COSMIIC-Inc/Implantables-PM-Hardware/Mechanical Design CAD Files/SolidWorks Native Files/NNP-DWG-115-005-000 SA, Battery.SLDASM

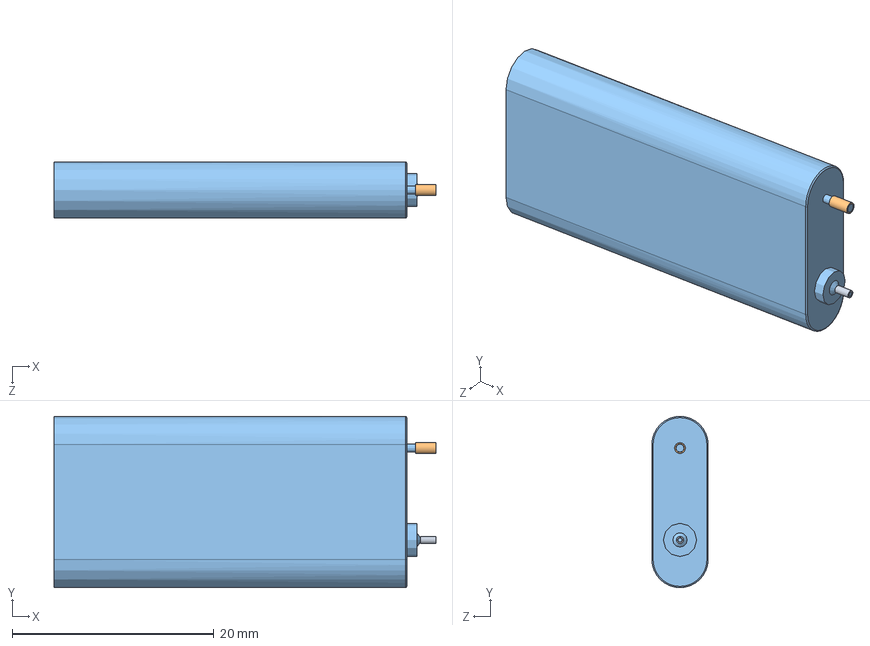
[picture p15: CAD file, 2024-08-27]
Mechanical Design CAD Files/SolidWorks Native Files/NNP-DWG-115-005-000 SA, Battery.SLDASM
37.9 x 17.0 x 5.59 mm
NNP-DWG-110-023-000 Battery, Quallion
NNP-DWG-110-024-001 Battery, Large Sleeve
NNP-DWG-110-024-002 Battery, Small Sleeve
