COSMIIC-Inc/Implantables-PM-Hardware/Mechanical Design CAD Files/SolidWorks Native Files/NNP-DWG-130-011-000 Balseal, Conductor.SLDPRT

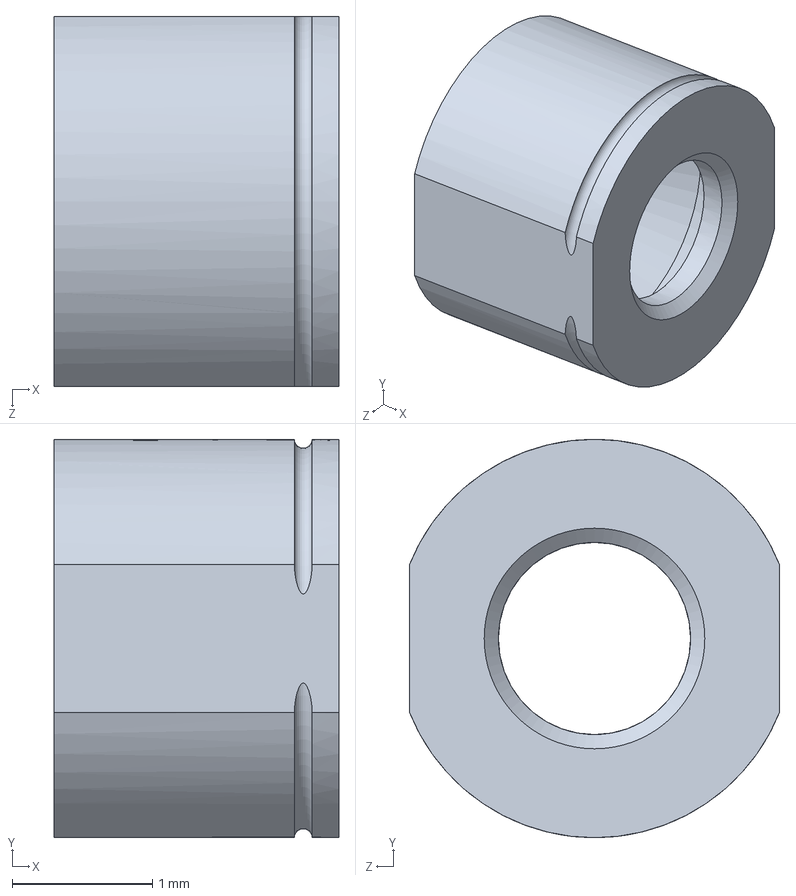
[picture p18: CAD file, 2024-08-27]
Mechanical Design CAD Files/SolidWorks Native Files/NNP-DWG-130-011-000 Balseal, Conductor.SLDPRT
2.03 x 2.84 x 2.64 mm
