COSMIIC-Inc/Implantables-PM-Hardware/Mechanical Design CAD Files/STEP Files/NNP-MAT-150-009-000 NuSil Med1-4213.STEP

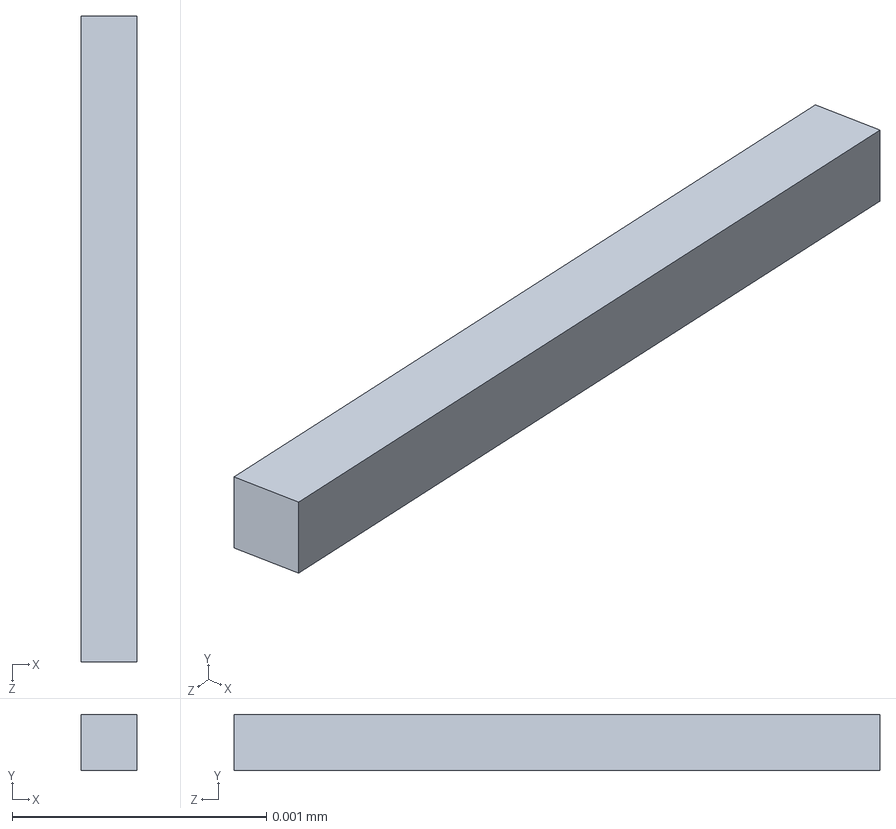
[picture p19: CAD file, 2024-08-27]
Mechanical Design CAD Files/STEP Files/NNP-MAT-150-009-000 NuSil Med1-4213.STEP
0.000221 x 0.000221 x 0.00254 mm
