COSMIIC-Inc/Implantables-PM-Hardware/Mechanical Design CAD Files/STEP Files/NNP-DWG-110-019-000 Capacitor, 0.47 uF.STEP

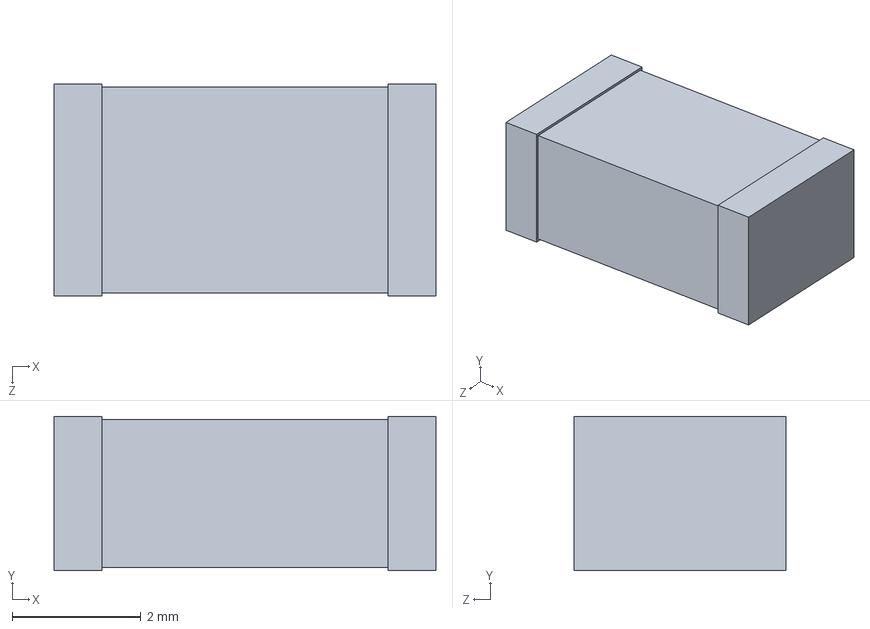
[picture p20: CAD file, 2024-08-27]
Mechanical Design CAD Files/STEP Files/NNP-DWG-110-019-000 Capacitor, 0.47 uF.STEP
5.94 x 2.40 x 3.30 mm
