COSMIIC-Inc/Implantables-PM-Hardware/Mechanical Design CAD Files/SolidWorks Native Files/NNP-DWG-110-024-001 Battery, Large Sleeve.SLDPRT

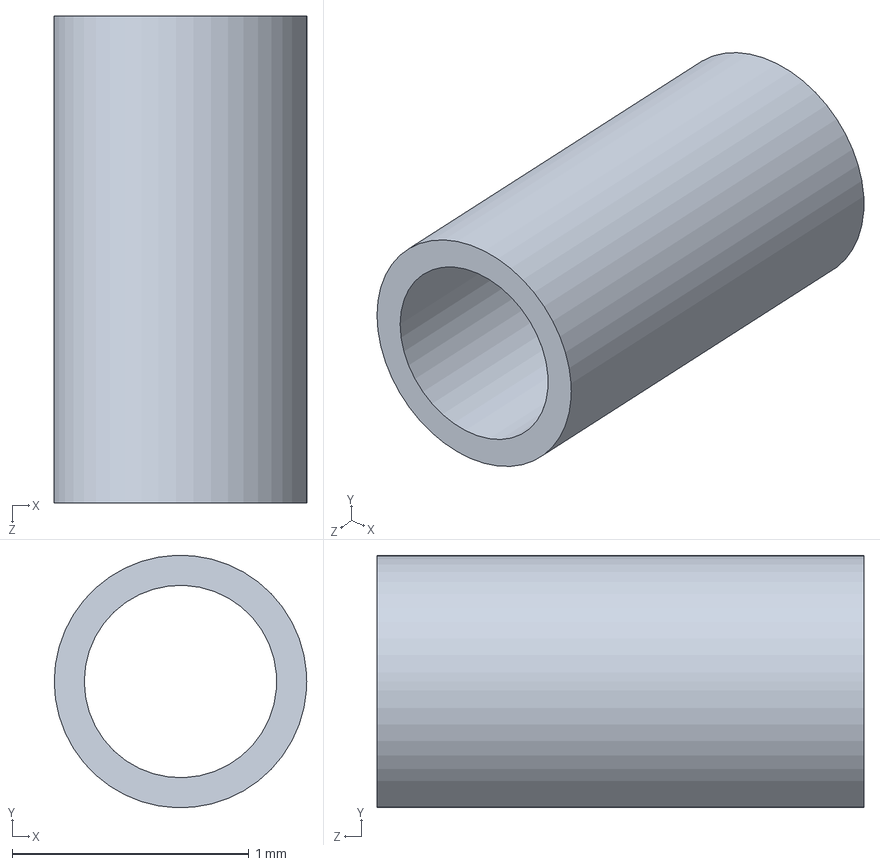
[picture p21: CAD file, 2024-08-27]
Mechanical Design CAD Files/SolidWorks Native Files/NNP-DWG-110-024-001 Battery, Large Sleeve.SLDPRT
1.07 x 1.07 x 2.06 mm
