COSMIIC-Inc/Implantables-PM-Hardware/Mechanical Design CAD Files/STEP Files/NNP-DWG-110-021-000 Insulator Nest, Top.STEP

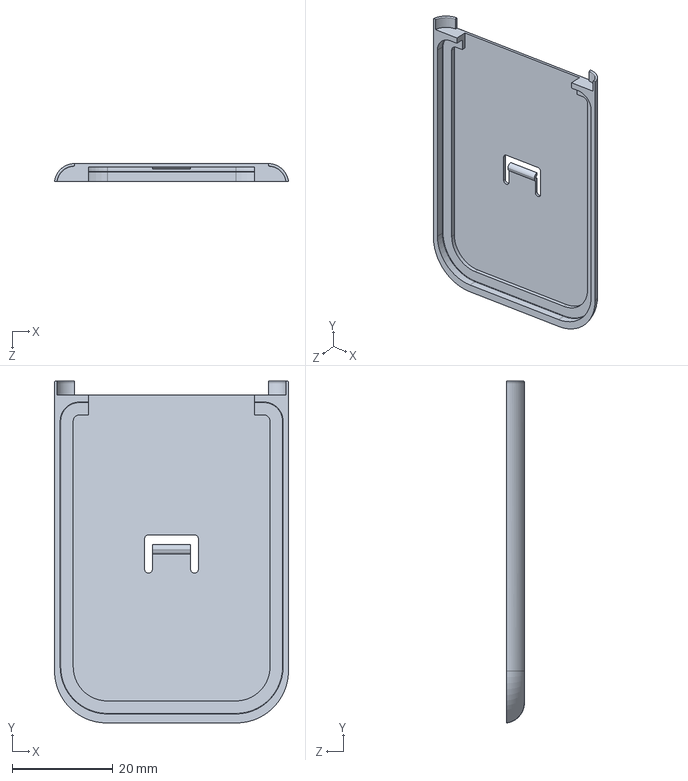
[picture p22: CAD file, 2024-08-27]
Mechanical Design CAD Files/STEP Files/NNP-DWG-110-021-000 Insulator Nest, Top.STEP
46.6 x 68.0 x 3.56 mm
