COSMIIC-Inc/Implantables-PM-Hardware/Mechanical Design CAD Files/SolidWorks Native Files/NNP-DWG-110-009-000 Case, Uncut Half.SLDPRT

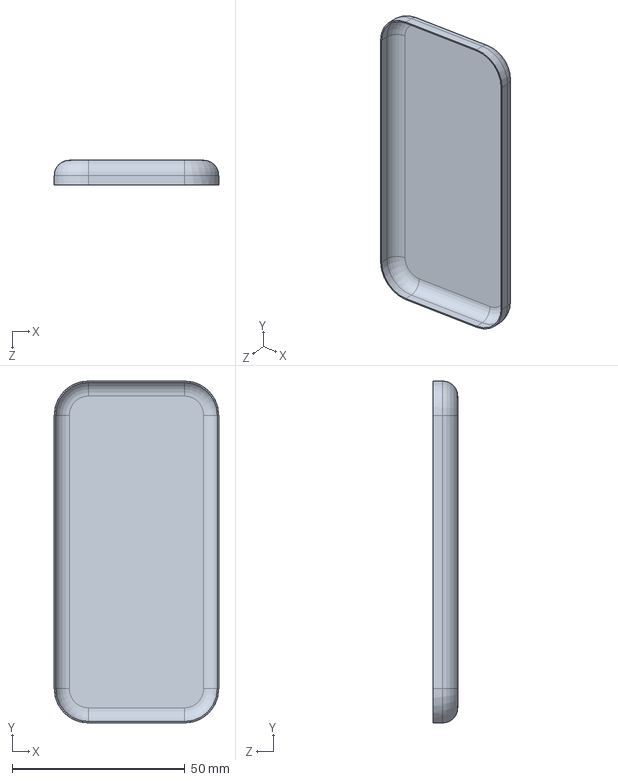
[picture p23: CAD file, 2024-08-27]
Mechanical Design CAD Files/SolidWorks Native Files/NNP-DWG-110-009-000 Case, Uncut Half.SLDPRT
47.7 x 99.1 x 7.11 mm
