COSMIIC-Inc/Implantables-PM-Hardware/Mechanical Design CAD Files/SolidWorks Native Files/NNP-DWG-110-013-000 Feedthrough Pin, Short.SLDPRT

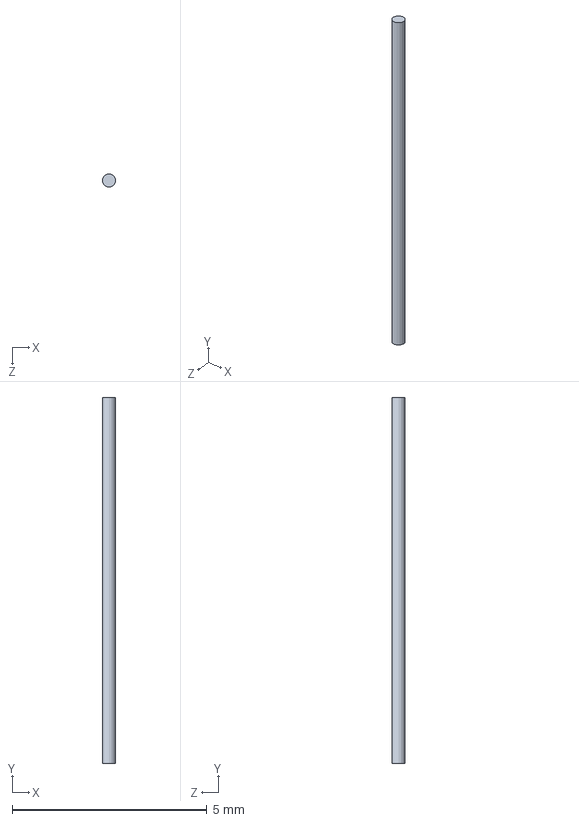
[picture p24: CAD file, 2024-08-27]
Mechanical Design CAD Files/SolidWorks Native Files/NNP-DWG-110-013-000 Feedthrough Pin, Short.SLDPRT
0.343 x 9.40 x 0.343 mm
