COSMIIC-Inc/Implantables-PM-Hardware/Mechanical Design CAD Files/STEP Files/NNP-DWG-110-008-000 BalSeal Block.STEP

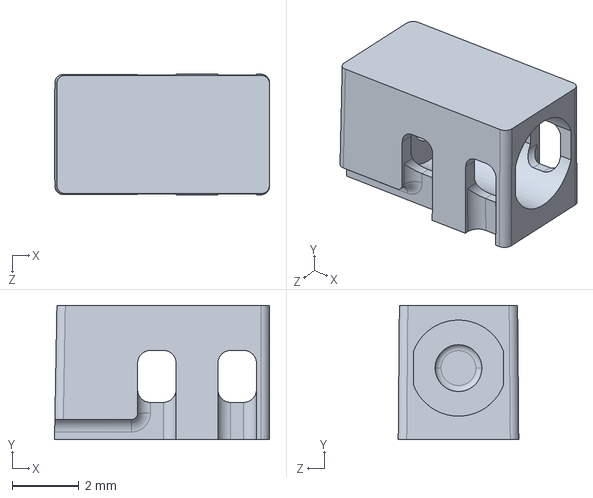
[picture p25: CAD file, 2024-08-27]
Mechanical Design CAD Files/STEP Files/NNP-DWG-110-008-000 BalSeal Block.STEP
6.42 x 4.01 x 3.60 mm
