COSMIIC-Inc/Implantables-PM-Hardware/Mechanical Design CAD Files/SolidWorks Native Files/NNP-DWG-110-003-000 Suture Skirt.SLDPRT

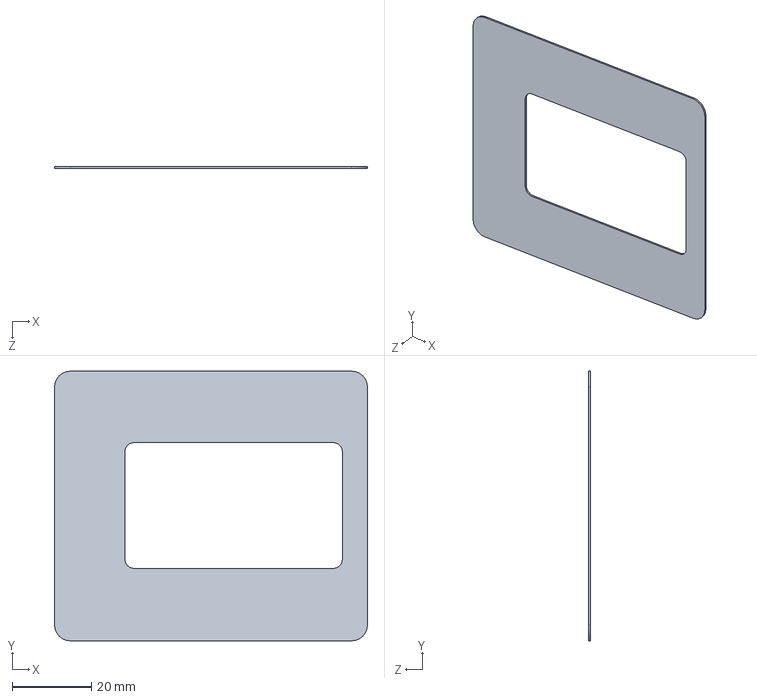
[picture p26: CAD file, 2024-08-27]
Mechanical Design CAD Files/SolidWorks Native Files/NNP-DWG-110-003-000 Suture Skirt.SLDPRT
79.0 x 68.1 x 0.5 mm
