COSMIIC-Inc/Implantables-PM-Hardware/Mechanical Design CAD Files/STEP Files/NNP-DWG-110-017-000 Power Module, Daughter Board.STEP

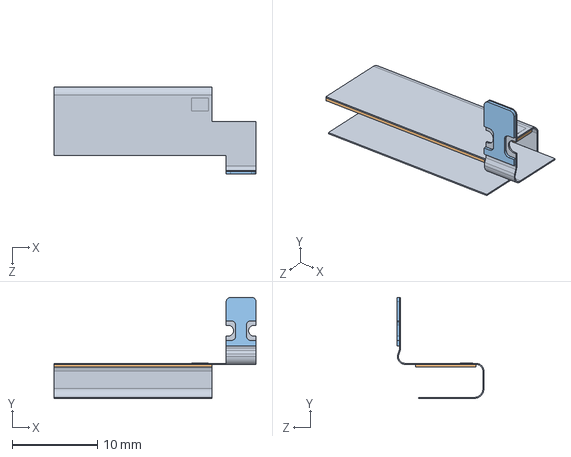
[picture p27: CAD file, 2024-08-27]
Mechanical Design CAD Files/STEP Files/NNP-DWG-110-017-000 Power Module, Daughter Board.STEP
23.7 x 11.9 x 10.2 mm
