COSMIIC-Inc/Implantables-PM-Hardware/Mechanical Design CAD Files/SolidWorks Native Files/NNP-DWG-110-020-000 Thermistor.SLDPRT

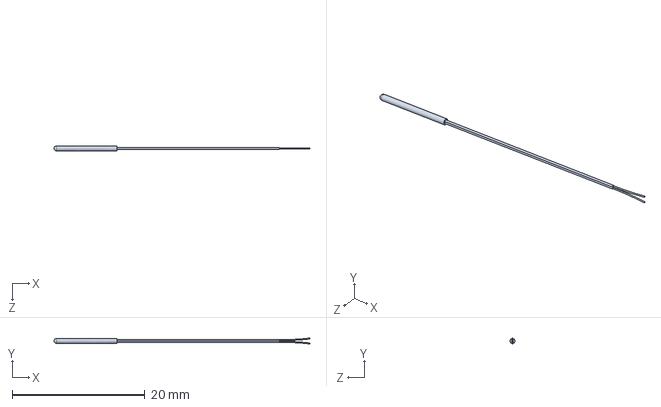
[picture p28: CAD file, 2024-08-27]
Mechanical Design CAD Files/SolidWorks Native Files/NNP-DWG-110-020-000 Thermistor.SLDPRT
38.6 x 0.891 x 0.761 mm
