COSMIIC-Inc/Implantables-PM-Hardware/Mechanical Design CAD Files/STEP Files/NNP-DWG-110-025-000 Recharge Coil.STEP

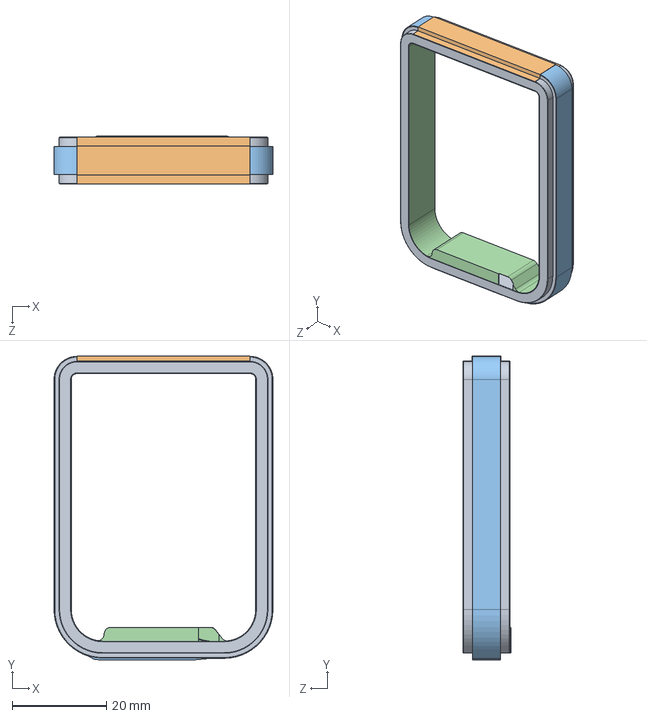
[picture p29: CAD file, 2024-08-27]
Mechanical Design CAD Files/STEP Files/NNP-DWG-110-025-000 Recharge Coil.STEP
46.5 x 64.5 x 10.2 mm
