COSMIIC-Inc/Implantables-PM-Hardware/Mechanical Design CAD Files/SolidWorks Native Files/NNP-DWG-110-015-000 Insulator, PM Feedthrough.SLDPRT

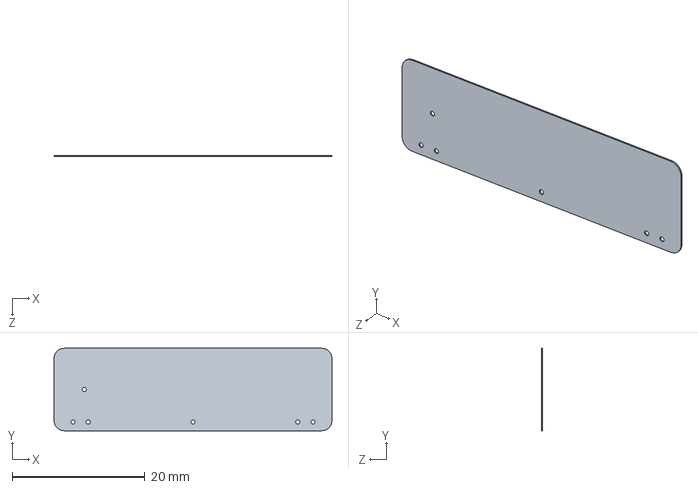
[picture p30: CAD file, 2024-08-27]
Mechanical Design CAD Files/SolidWorks Native Files/NNP-DWG-110-015-000 Insulator, PM Feedthrough.SLDPRT
41.9 x 12.4 x 0.19 mm
