COSMIIC-Inc/Implantables-PM-Hardware/Mechanical Design CAD Files/STEP Files/NNP-DWG-130-012-002 Balseal, Spring, CCW.STEP

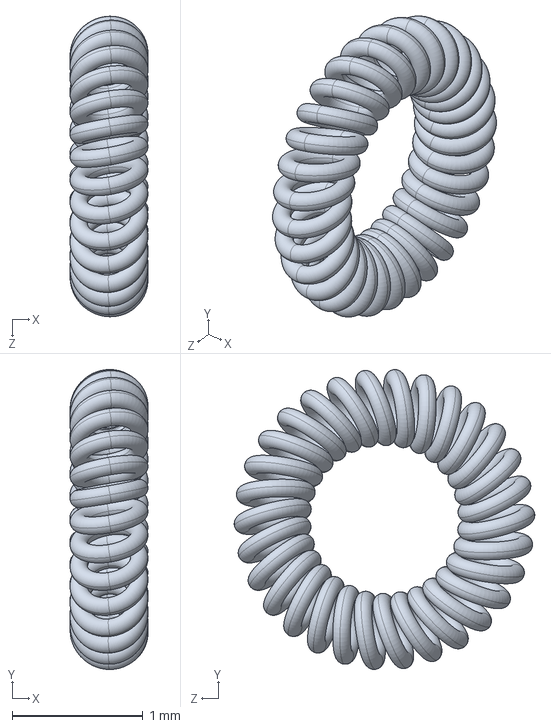
[picture p31: CAD file, 2024-08-27]
Mechanical Design CAD Files/STEP Files/NNP-DWG-130-012-002 Balseal, Spring, CCW.STEP
0.597 x 2.30 x 2.30 mm
