COSMIIC-Inc/Implantables-PM-Hardware/Mechanical Design CAD Files/SolidWorks Native Files/NNP-DWG-110-002-000 Port Plug, Body.SLDPRT

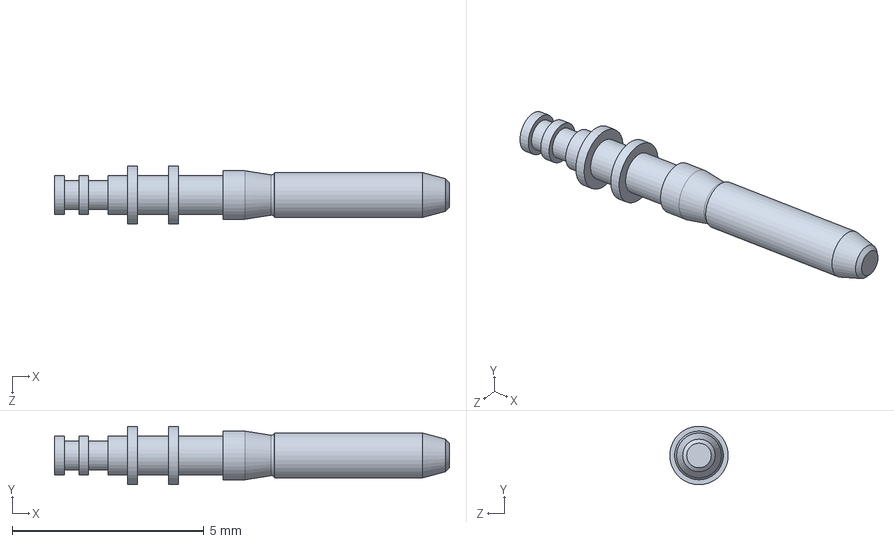
[picture p32: CAD file, 2024-08-27]
Mechanical Design CAD Files/SolidWorks Native Files/NNP-DWG-110-002-000 Port Plug, Body.SLDPRT
10.3 x 1.52 x 1.52 mm
