COSMIIC-Inc/Implantables-PM-Hardware/Mechanical Design CAD Files/SolidWorks Native Files/NNP-DWG-110-012-000 Lidthrough, Anchor Pin.SLDPRT

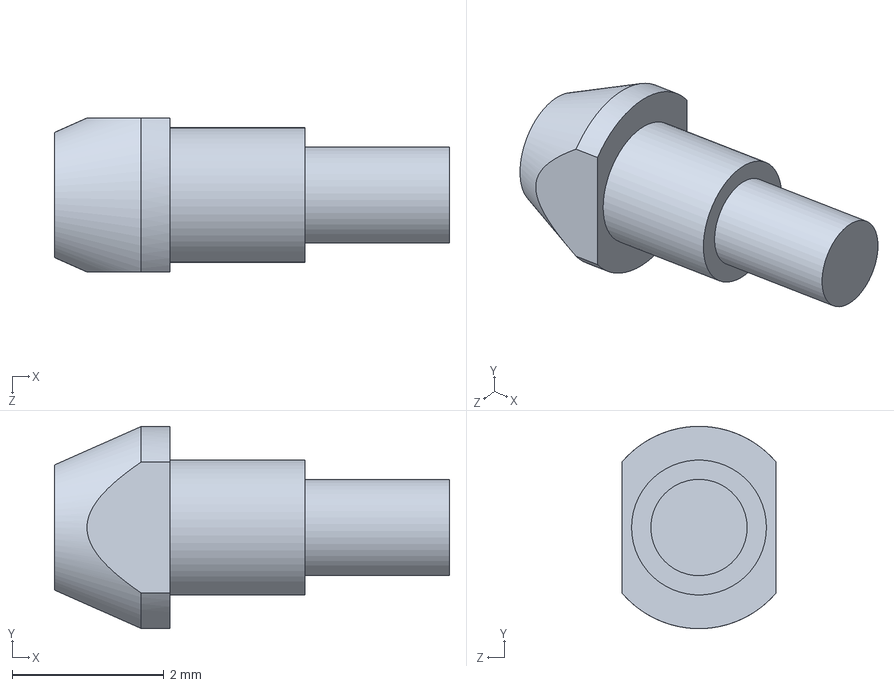
[picture p33: CAD file, 2024-08-27]
Mechanical Design CAD Files/SolidWorks Native Files/NNP-DWG-110-012-000 Lidthrough, Anchor Pin.SLDPRT
5.21 x 2.67 x 2.03 mm
