COSMIIC-Inc/Implantables-PM-Hardware/Mechanical Design CAD Files/STEP Files/NNP-DWG-110-022-000 Insulator Nest, Bottom.STEP

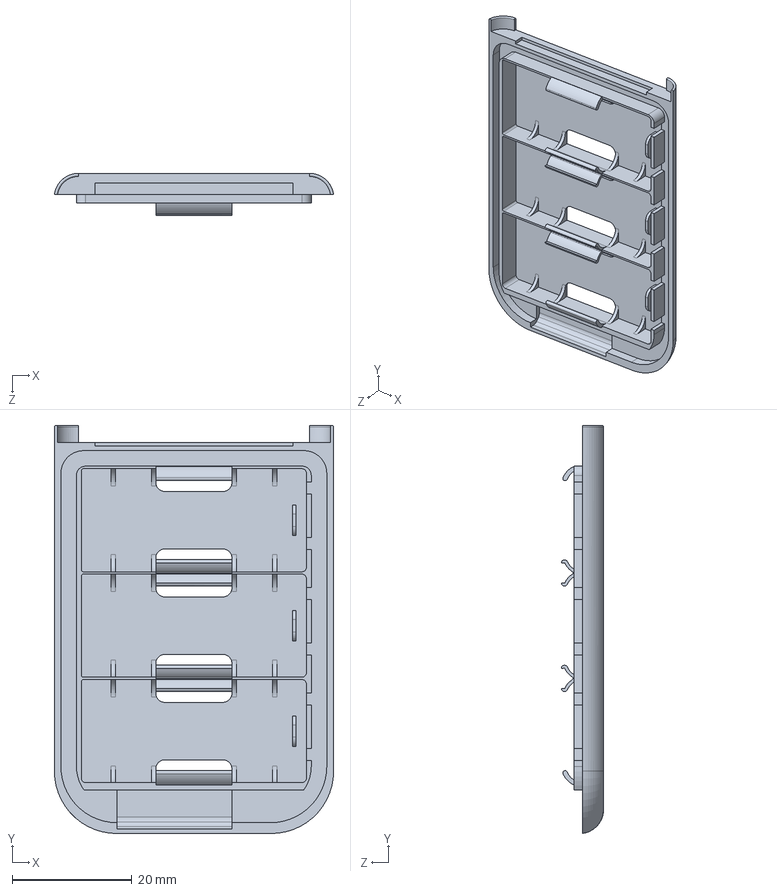
[picture p34: CAD file, 2024-08-27]
Mechanical Design CAD Files/STEP Files/NNP-DWG-110-022-000 Insulator Nest, Bottom.STEP
46.6 x 68.0 x 7.07 mm
