COSMIIC-Inc/Implantables-PM-Hardware/Mechanical Design CAD Files/SolidWorks Native Files/NNP-MAT-150-015-000 Kapton Tape.SLDPRT

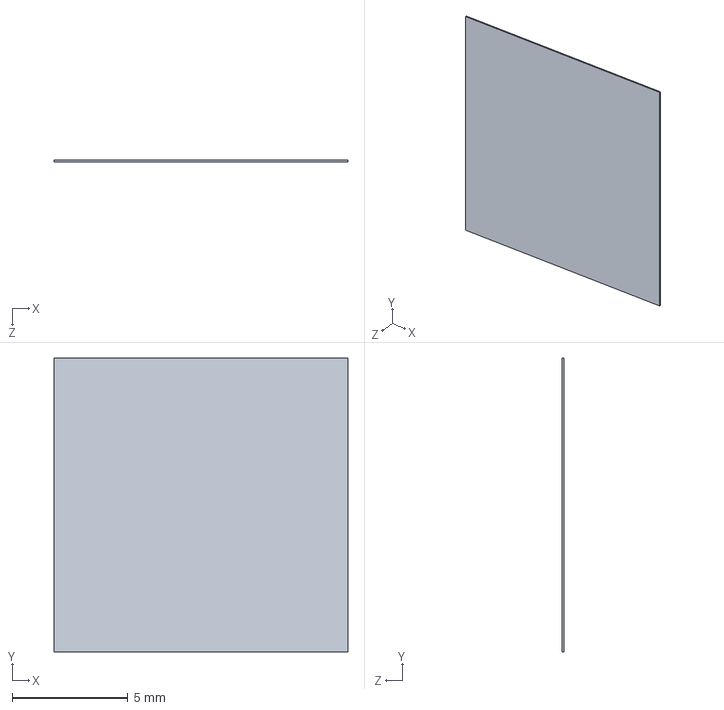
[picture p35: CAD file, 2024-08-27]
Mechanical Design CAD Files/SolidWorks Native Files/NNP-MAT-150-015-000 Kapton Tape.SLDPRT
12.7 x 12.7 x 0.07 mm
