COSMIIC-Inc/Implantables-PM-Hardware/Mechanical Design CAD Files/STEP Files/NNP-DWG-110-014-000 Lidthrough, Flange, 2 Port, Kryoflex.STEP

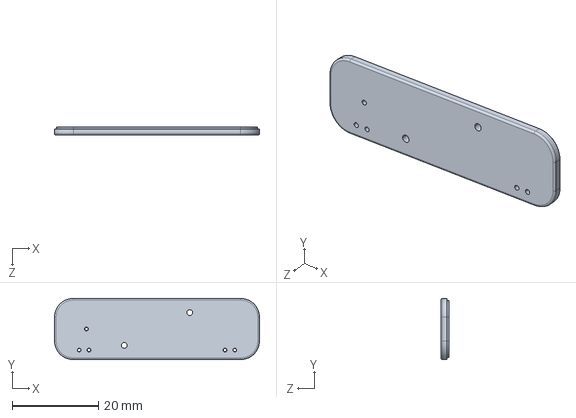
[picture p36: CAD file, 2024-08-27]
Mechanical Design CAD Files/STEP Files/NNP-DWG-110-014-000 Lidthrough, Flange, 2 Port, Kryoflex.STEP
47.7 x 14.2 x 1.91 mm
