COSMIIC-Inc/Implantables-PM-Hardware/Mechanical Design CAD Files/STEP Files/NNP-DWG-110-010-000 Case, Trimmed.STEP

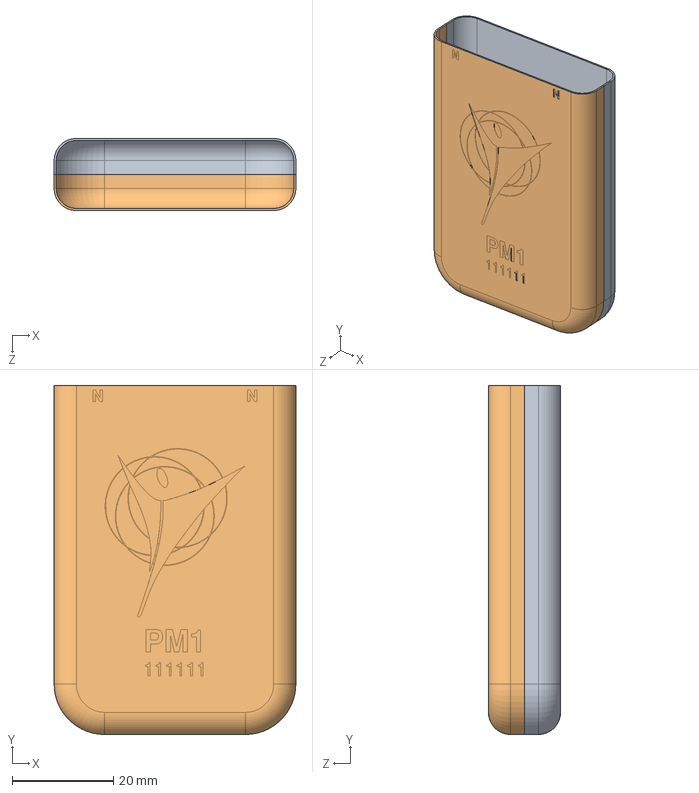
[picture p37: CAD file, 2024-08-27]
Mechanical Design CAD Files/STEP Files/NNP-DWG-110-010-000 Case, Trimmed.STEP
47.7 x 68.8 x 14.2 mm
NNP-DWG-110-009-000 Case, Uncut Half
NNP-DWG-110-009-000 Case, Uncut Half_Front Artwork
