COSMIIC-Inc/Implantables-PM-Hardware/Mechanical Design CAD Files/SolidWorks Native Files/NNP-DWG-110-005-000 Antenna Wire.SLDPRT

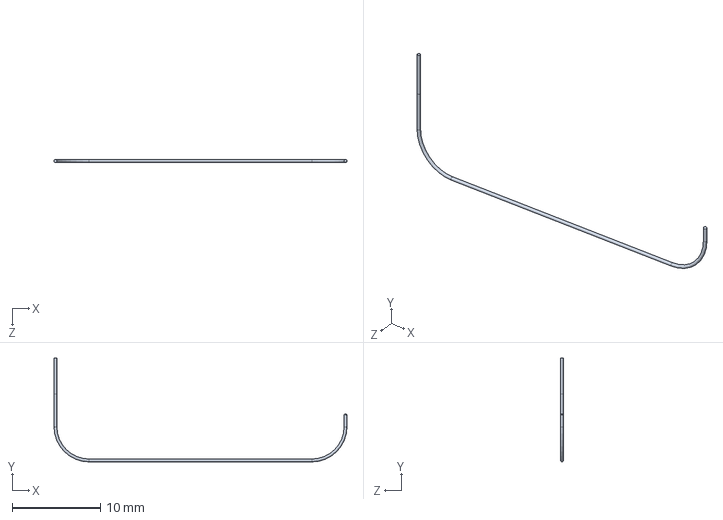
[picture p38: CAD file, 2024-08-27]
Mechanical Design CAD Files/SolidWorks Native Files/NNP-DWG-110-005-000 Antenna Wire.SLDPRT
33.2 x 11.8 x 0.33 mm
