COSMIIC-Inc/Implantables-PM-Hardware/Mechanical Design CAD Files/SolidWorks Native Files/NNP-DWG-110-016-000 Pre-Molded Header, 2-Port.SLDPRT

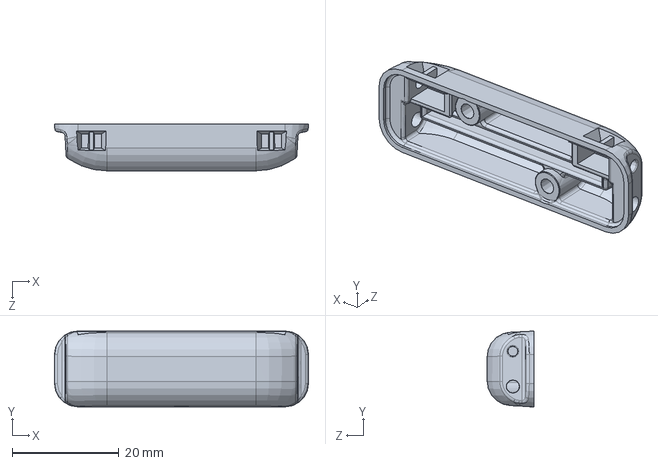
[picture p39: CAD file, 2024-08-27]
Mechanical Design CAD Files/SolidWorks Native Files/NNP-DWG-110-016-000 Pre-Molded Header, 2-Port.SLDPRT
47.7 x 14.2 x 8.76 mm
