COSMIIC-Inc/Implantables-PM-Hardware/Mechanical Design CAD Files/STEP Files/NNP-DWG-110-018-000 Capacitor, 0.22 uF.STEP

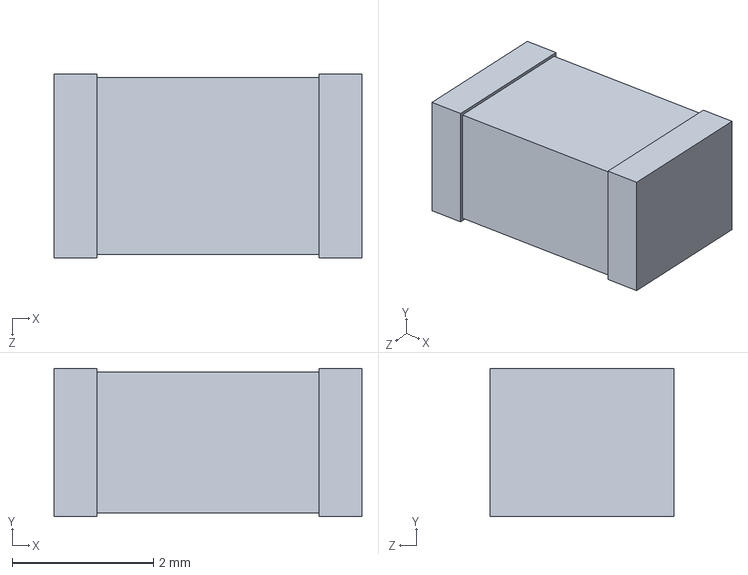
[picture p40: CAD file, 2024-08-27]
Mechanical Design CAD Files/STEP Files/NNP-DWG-110-018-000 Capacitor, 0.22 uF.STEP
4.36 x 2.10 x 2.60 mm
