COSMIIC-Inc/Implantables-PM-Hardware/Mechanical Design CAD Files/SolidWorks Native Files/NNP-DWG-110-004-000 Antenna Support.SLDPRT

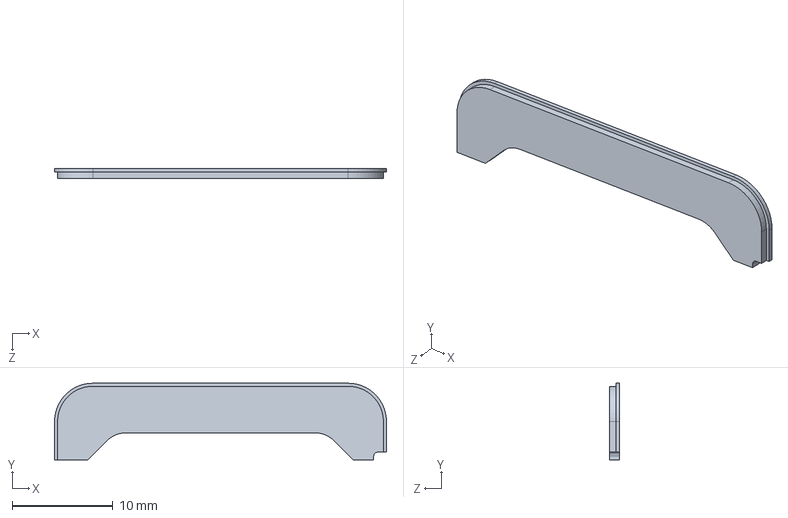
[picture p41: CAD file, 2024-08-27]
Mechanical Design CAD Files/SolidWorks Native Files/NNP-DWG-110-004-000 Antenna Support.SLDPRT
33.0 x 7.62 x 1.02 mm
