COSMIIC-Inc/Implantables-PM-Hardware/Mechanical Design CAD Files/SolidWorks Native Files/NNP-DWG-110-006-000 Case, Connection Wire.SLDPRT

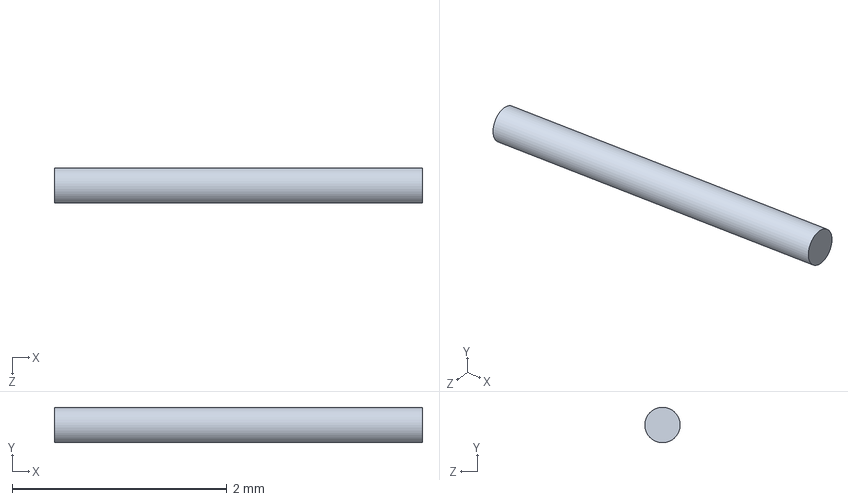
[picture p42: CAD file, 2024-08-27]
Mechanical Design CAD Files/SolidWorks Native Files/NNP-DWG-110-006-000 Case, Connection Wire.SLDPRT
3.43 x 0.33 x 0.33 mm
