COSMIIC-Inc/Implantables-PM-Hardware/Mechanical Design CAD Files/STEP Files/NNP-DWG-135-002-000 SA, Balseal, CW.STEP

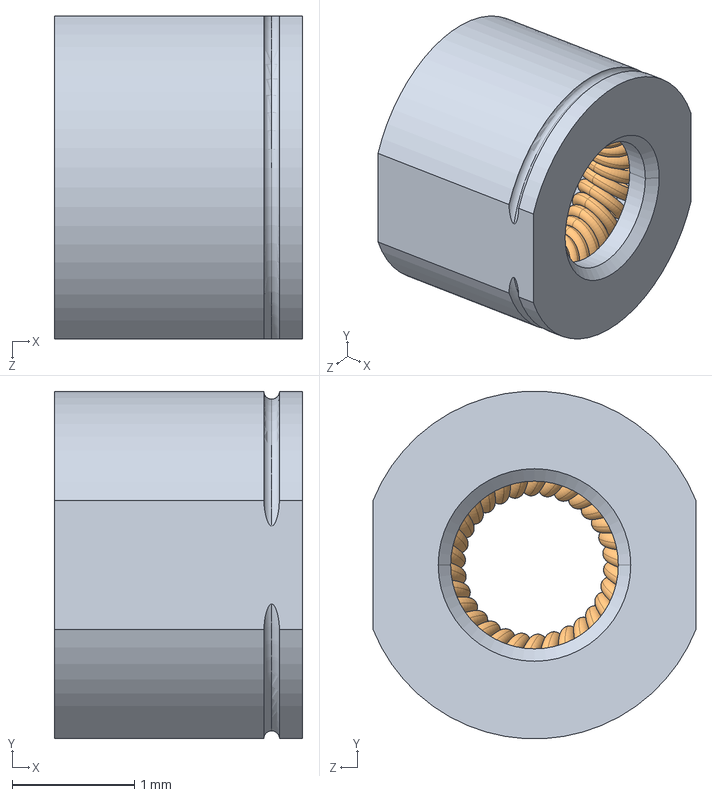
[picture p43: CAD file, 2024-08-27]
Mechanical Design CAD Files/STEP Files/NNP-DWG-135-002-000 SA, Balseal, CW.STEP
2.03 x 2.84 x 2.64 mm
NNP-DWG-130-011-000 Balseal, Conductor
NNP-DWG-130-012-001 Balseal, Spring, CW
NNP-DWG-130-013-001 Balseal, Washer, CW
