COSMIIC-Inc/Implantables-PM-Hardware/Mechanical Design CAD Files/STEP Files/NNP-DWG-110-007-000 Silicone Tube.STEP

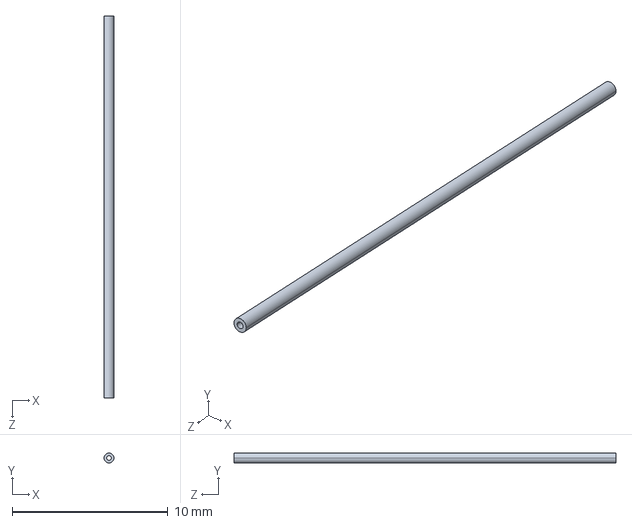
[picture p44: CAD file, 2024-08-27]
Mechanical Design CAD Files/STEP Files/NNP-DWG-110-007-000 Silicone Tube.STEP
0.635 x 0.635 x 24.5 mm
