COSMIIC-Inc/Implantables-PM-Hardware/Mechanical Design CAD Files/STEP Files/NNP-DWG-110-024-002 Battery, Small Sleeve.STEP

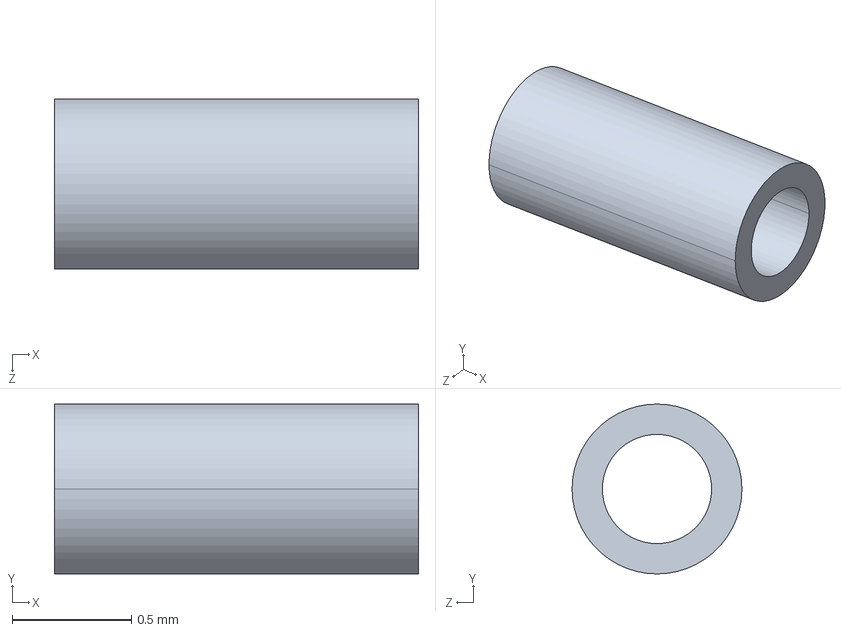
[picture p45: CAD file, 2024-08-27]
Mechanical Design CAD Files/STEP Files/NNP-DWG-110-024-002 Battery, Small Sleeve.STEP
1.52 x 0.711 x 0.711 mm
