COSMIIC-Inc/Implantables-PM-Hardware/Mechanical Design CAD Files/SolidWorks Native Files/NNP-DWG-110-007-000 Silicone Tube.SLDPRT

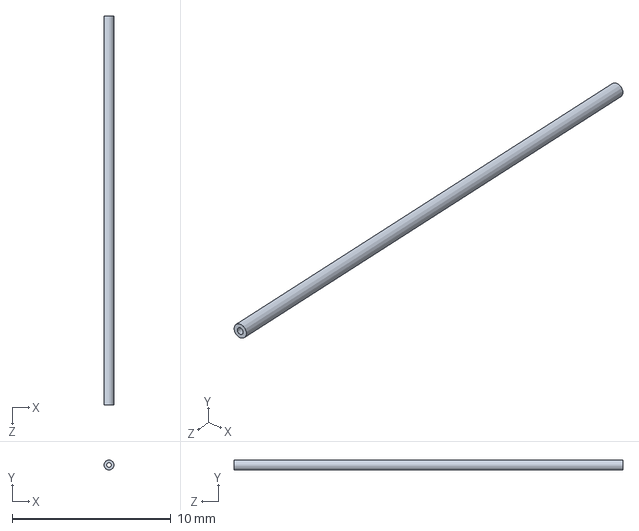
[picture p46: CAD file, 2024-08-27]
Mechanical Design CAD Files/SolidWorks Native Files/NNP-DWG-110-007-000 Silicone Tube.SLDPRT
0.635 x 0.632 x 24.5 mm
