COSMIIC-Inc/Implantables-PM-Hardware/Mechanical Design CAD Files/SolidWorks Native Files/NNP-DWG-110-021-000 Insulator Nest, Top.SLDPRT

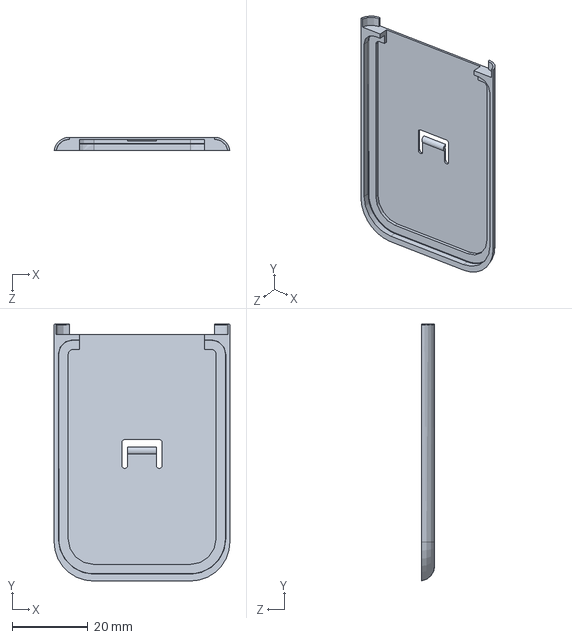
[picture p47: CAD file, 2024-08-27]
Mechanical Design CAD Files/SolidWorks Native Files/NNP-DWG-110-021-000 Insulator Nest, Top.SLDPRT
46.6 x 68.0 x 3.56 mm
