COSMIIC-Inc/Implantables-PM-Hardware/Mechanical Design CAD Files/SolidWorks Native Files/NNP-DWG-110-024-002 Battery, Small Sleeve.SLDPRT

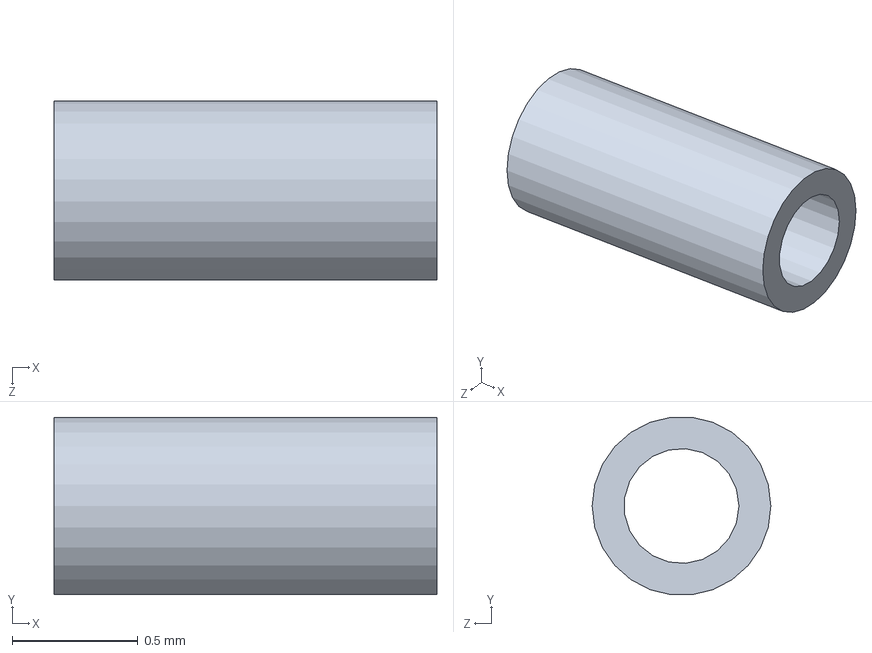
[picture p48: CAD file, 2024-08-27]
Mechanical Design CAD Files/SolidWorks Native Files/NNP-DWG-110-024-002 Battery, Small Sleeve.SLDPRT
1.52 x 0.706 x 0.711 mm
