COSMIIC-Inc/Implantables-PM-Hardware/Mechanical Design CAD Files/SolidWorks Native Files/NNP-DWG-135-002-000 SA, Balseal, CW.SLDASM

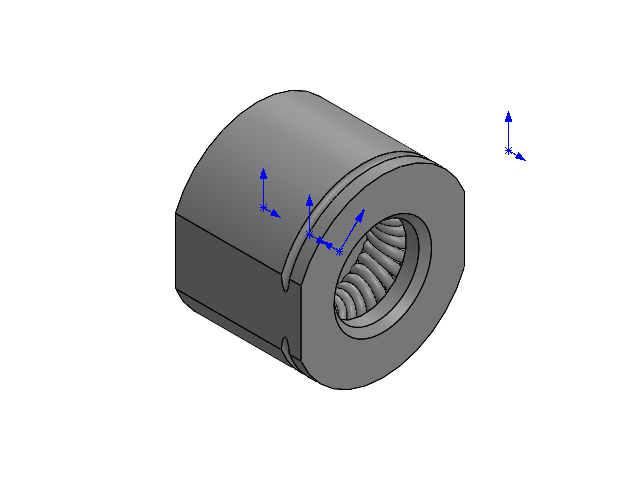
[picture p50: CAD file, 2024-08-27]
Mechanical Design CAD Files/SolidWorks Native Files/NNP-DWG-135-002-000 SA, Balseal, CW.SLDASM
NNP-DWG-130-011-000 Balseal, Conductor
NNP-DWG-130-012-001 Balseal, Spring, CW
NNP-DWG-130-013-001 Balseal, Washer, CW
