COSMIIC-Inc/Implantables-PM-Hardware/NNP-DWG-115-004-000 PCB Files/NNP-DWG-115-004-000 PM2 Schematics/51-2001-01-2_04 Power Module Schematic.pdf

ECN | DESCRIPTION | REV | DATE | REV. SHT. DWG. NO.

# ANALOG SIGNALS

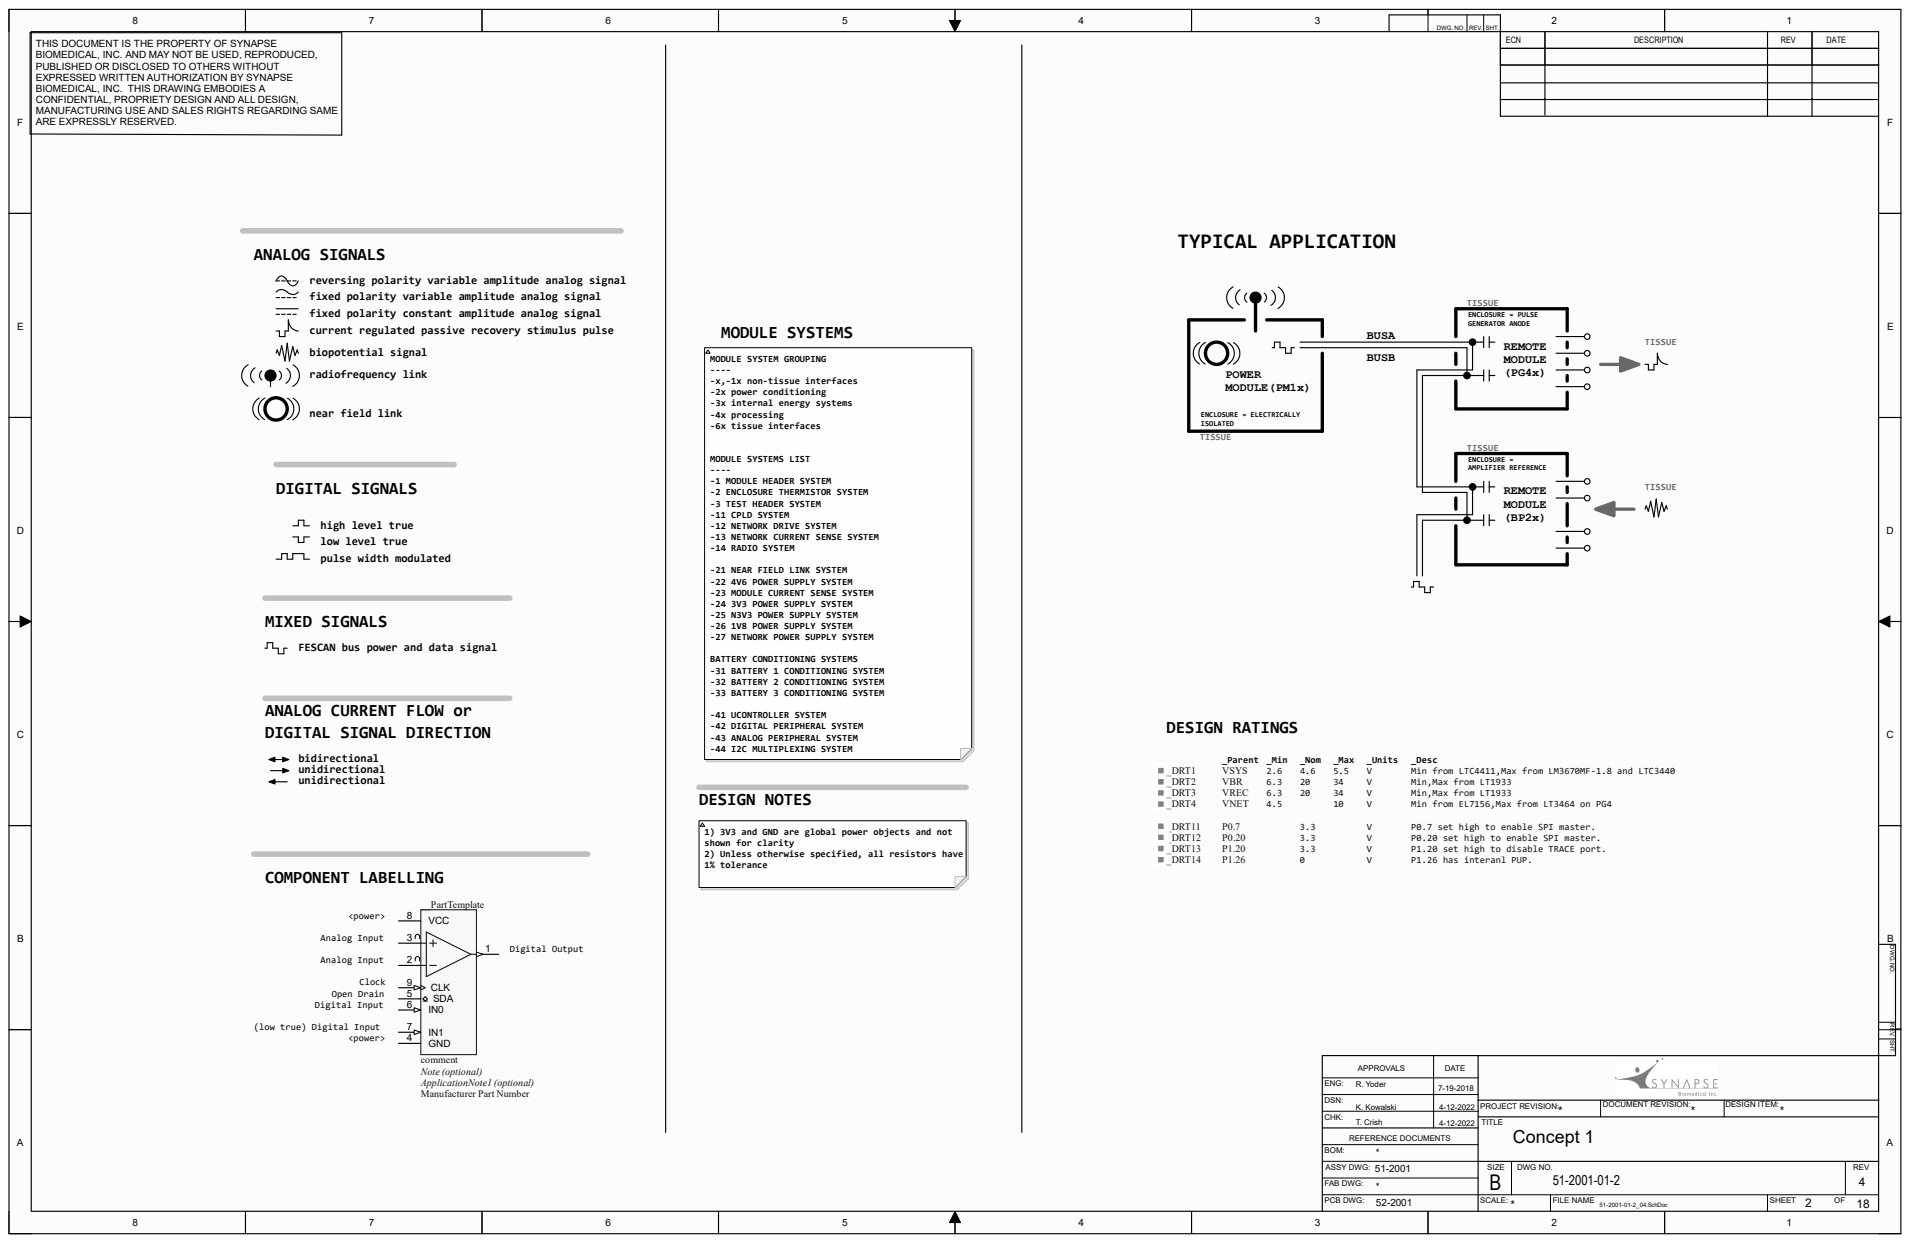
[picture p60: page 1]
Concept 1; 51-2001-01-2_04.SchDoc; TITLE; SIZE; DWG NO.; FILE NAME; SHEET; REV; SCALE:*; REFERENCE DOCUMENTS; BOM:; ASSY DWG:; FAB DWG:; PCB DWG:; VCC 8; GND 4; Analog Input; Digital Output; SDA Open Drain; IN0 Digital Input; <power>; IN1 (low true) Digital Input; CLK Clock; __PartTemplate; COMPONENT LABELLING; _Parent; _Max _Units _Desc _Min _Nom; DESIGN RATINGS; DIGITAL SIGNALS; bidirectional unidirectional unidirectional; MIXED SIGNALS; DESIGN NOTES; MODULE SYSTEMS; POWER MODULE(PM1x)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

DWG. NO. | REV. | SHT.

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

reversing polarity variable amplitude analog signal
fixed polarity variable amplitude analog signal
fixed polarity constant amplitude analog signal
current regulated passive recovery stimulus pulse
biopotential signal
radiofrequency link

MODULE SYSTEM GROUPING
-x,-1x non-tissue interfaces
-2x power conditioning
-3x internal energy systems
-4x processing
-6x tissue interfaces

near field link

MODULE SYSTEMS LIST
-1 MODULE HEADER SYSTEM
-2 ENCLOSURE THERMISTOR SYSTEM
-3 TEST HEADER SYSTEM
-11 CPLD SYSTEM
-12 NETWORK DRIVE SYSTEM
-13 NETWORK CURRENT SENSE SYSTEM
-14 RADIO SYSTEM

high level true
low level true
pulse width modulated

-21 NEAR FIELD LINK SYSTEM
-22 4V6 POWER SUPPLY SYSTEM
-23 MODULE CURRENT SENSE SYSTEM
-24 3V3 POWER SUPPLY SYSTEM
-25 N3V3 POWER SUPPLY SYSTEM
-26 1V8 POWER SUPPLY SYSTEM
-27 NETWORK POWER SUPPLY SYSTEM

FESCAN bus power and data signal

BATTERY CONDITIONING SYSTEMS
-31 BATTERY 1 CONDITIONING SYSTEM
-32 BATTERY 2 CONDITIONING SYSTEM
-33 BATTERY 3 CONDITIONING SYSTEM

ANALOG CURRENT FLOW or
DIGITAL SIGNAL DIRECTION

-41 UCONTROLLER SYSTEM
-42 DIGITAL PERIPHERAL SYSTEM
-43 ANALOG PERIPHERAL SYSTEM
-44 I2C MULTIPLEXING SYSTEM

1) 3V3 and GND are global power objects and not
shown for clarity
2) Unless otherwise specified, all resistors have
1% tolerance

comment
Note (optional)
ApplicationNote1 (optional)
Manufacturer Part Number

APPROVALS | DATE

ENG: R. Yoder | 7-19-2018

DSN: K. Kowalski | 4-12-2022

PROJECT REVISION: * | DOCUMENT REVISION: * | DESIGN ITEM: *

CHK: T. Crish | 4-12-2022
