COSMIIC-Inc/Implantables-PM-Hardware/NNP-DWG-115-004-000 PCB Files/NNP-DWG-115-004-000 PM2 Schematics/51-2001-01-3_04 Power Module Schematic.pdf

ECN | DESCRIPTION | REV | DATE | REV. SHT. DWG. NO.

# BLOCK DIAGRAM

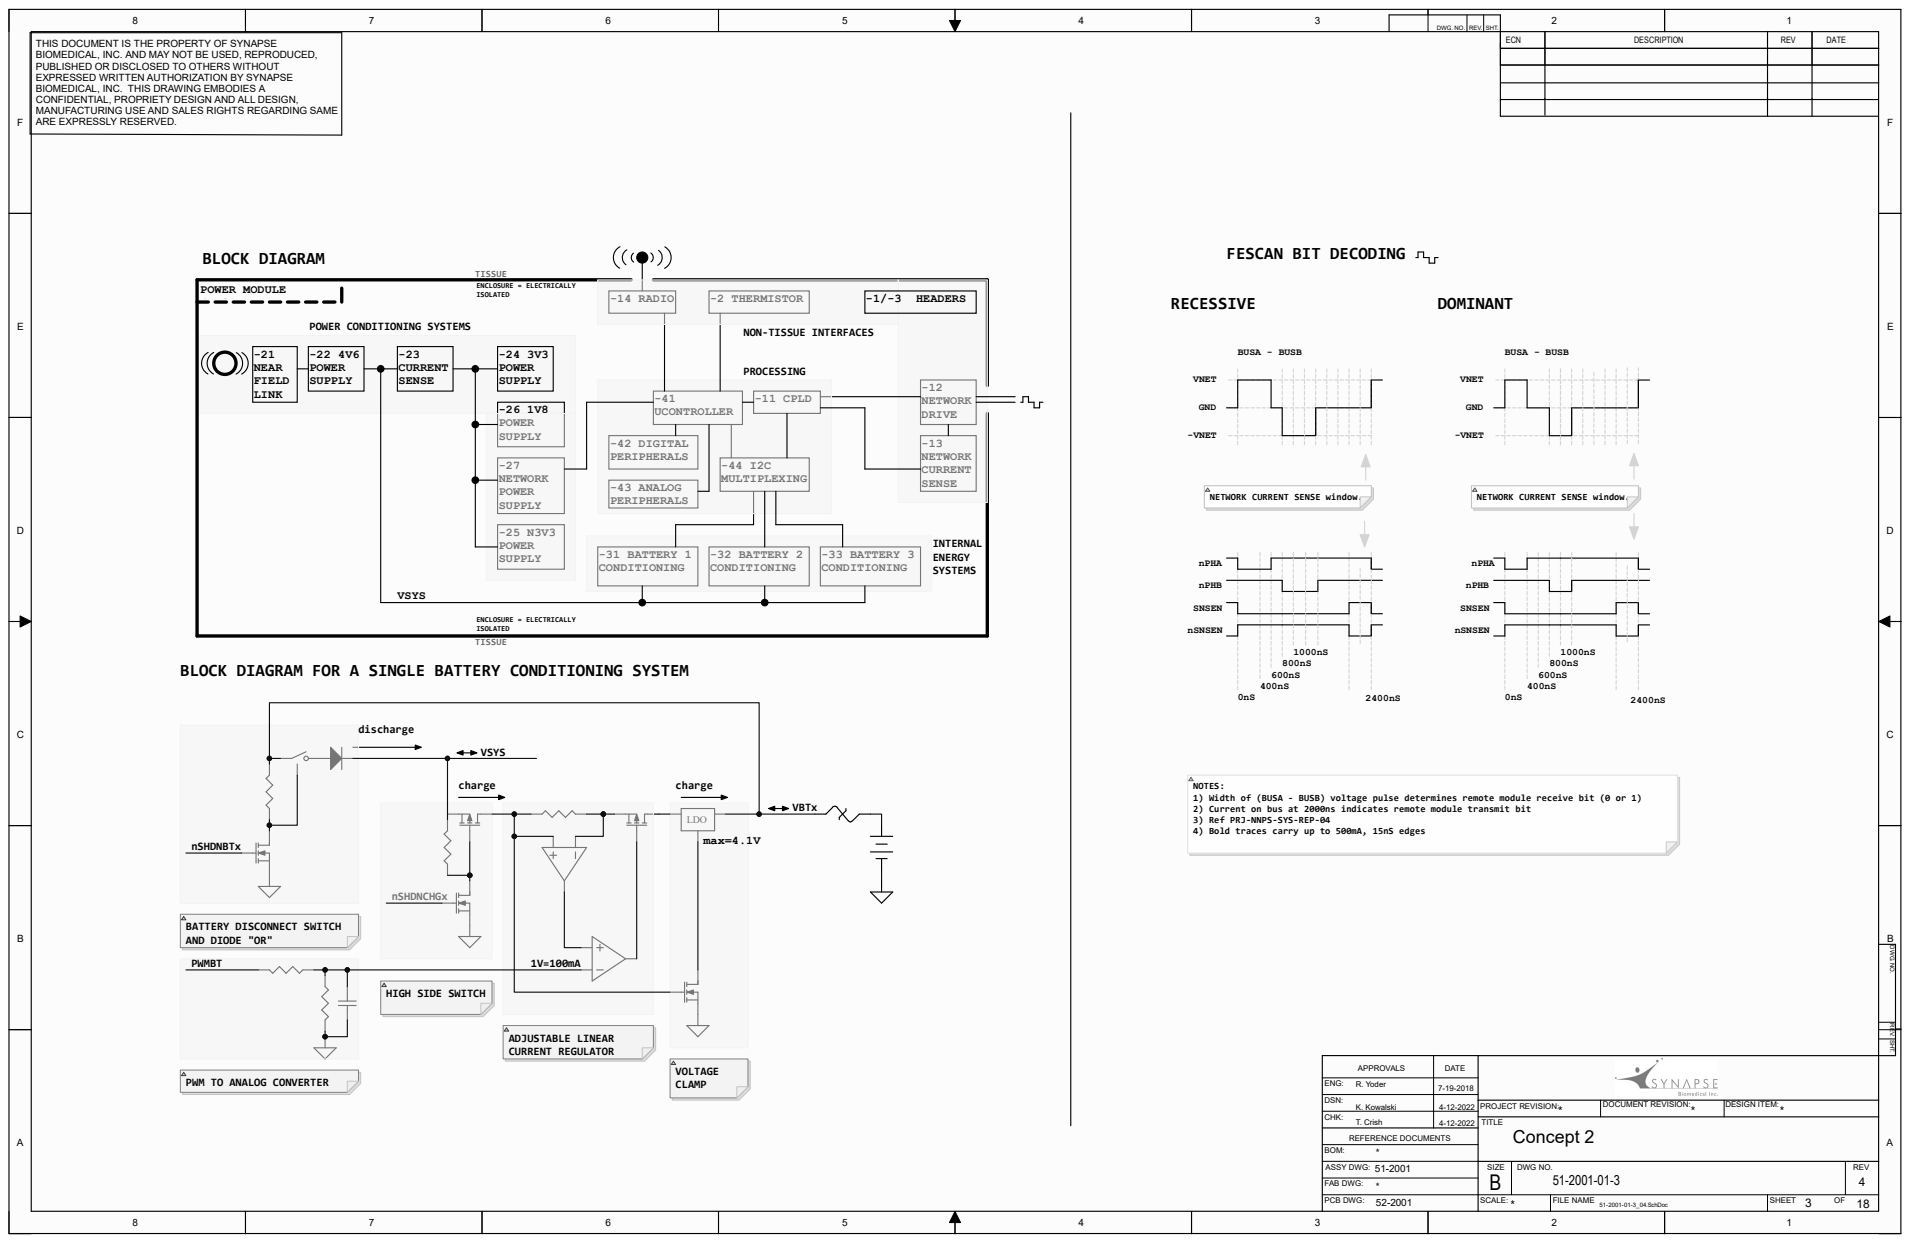
[picture p61: page 1]
Concept 2; 51-2001-01-3_04.SchDoc; TITLE; SIZE; DWG NO.; FILE NAME; SHEET; REV; SCALE:*; REFERENCE DOCUMENTS; BOM:; ASSY DWG:; FAB DWG:; PCB DWG:; TISSUE; -21 NEAR FIELD LINK; -22 4V6 POWER SUPPLY; -23 CURRENT SENSE; -24 3V3 POWER SUPPLY; -25 N3V3 POWER SUPPLY; -26 1V8 POWER SUPPLY; -27 NETWORK POWER SUPPLY; -31 BATTERY 1 CONDITIONING; -32 BATTERY 2 CONDITIONING; -33 BATTERY 3 CONDITIONING; -41 UCONTROLLER; -42 DIGITAL PERIPHERALS; -43 ANALOG PERIPHERALS; -44 I2C MULTIPLEXING; -11 CPLD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

DWG. NO. | REV. | SHT.

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

FESCAN BIT DECODING

NETWORK CURRENT SENSE window.

BLOCK DIAGRAM FOR A SINGLE BATTERY CONDITIONING SYSTEM

NOTES:
1) Width of (BUSA - BUSB) voltage pulse determines remote module receive bit (0 or 1)
2) Current on bus at 2000ns indicates remote module transmit bit
3) Ref PRJ-NNPS-SYS-REP-04
4) Bold traces carry up to 500mA, 15nS edges

BATTERY DISCONNECT SWITCH
AND DIODE "OR"

HIGH SIDE SWITCH

APPROVALS | DATE

PWM TO ANALOG CONVERTER

ENG: R. Yoder | 7-19-2018

DSN: K. Kowalski | 4-12-2022

PROJECT REVISION: * | DOCUMENT REVISION: * | DESIGN ITEM: *

CHK: T. Crish | 4-12-2022
