COSMIIC-Inc/Implantables-PM-Hardware/NNP-DWG-115-004-000 PCB Files/NNP-DWG-115-004-000 PM2 Schematics/51-2001-01-4_04 Power Module Schematic.pdf

ECN | DESCRIPTION | REV | DATE | REV. SHT. DWG. NO.
RADIO PWR & GND PLANES BUSA | BUSB | BUSB | BUSA nBOOT TXD⁰ | RXD⁰

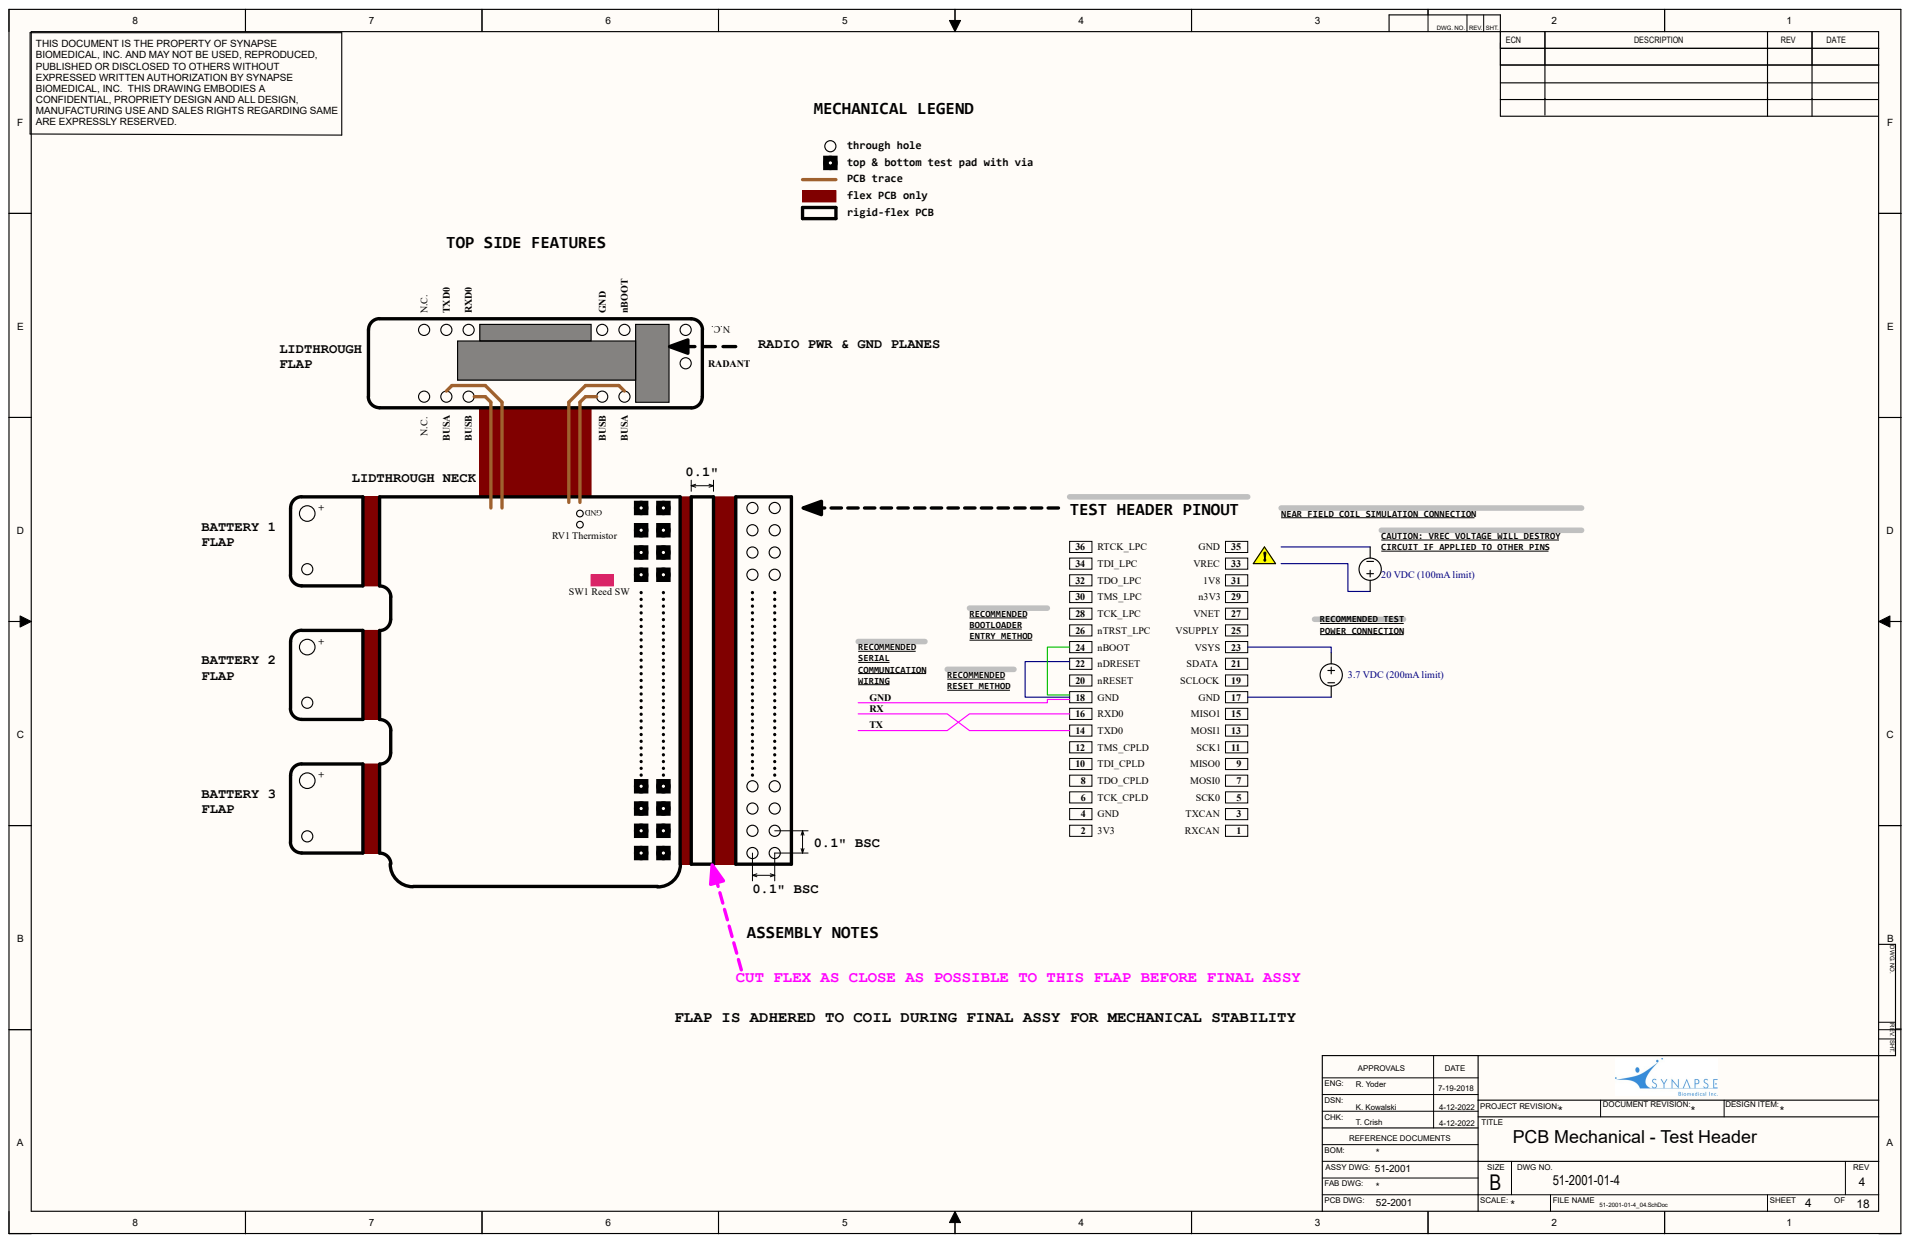
[picture p62: page 1]
51-2001-01-4_04.SchDoc; SIZE; DWG NO.; FILE NAME; SHEET; REV; SCALE:*; REFERENCE DOCUMENTS; BOM:; ASSY DWG:; FAB DWG:; PCB DWG:; BATTERY 1 FLAP; LIDTHROUGH FLAP; BATTERY 2 FLAP; BATTERY 3 FLAP; LIDTHROUGH NECK; RADANT N.C. N.C.; RTCK_LPC; TDI_LPC; TDO_LPC; TMS_LPC; TCK_LPC; nTRST_LPC; nBOOT; nDRESET; nRESET; GND; RXD0; TXD0; TMS_CPLD; TDI_CPLD; TDO_CPLD; TCK_CPLD; VREC; VNET; VSUPPLY; VSYS; SDATA; SCLOCK; MISO1; MOSI1; SCK1; MISO0; MOSI0; SCK0; TXCAN; RXCAN; 36 35 GND; RV1 Thermistor GND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

DWG. NO. | REV. | SHT.

THIS DOCUMENT IS THE PROPERTY OF SYNAPSE BIOMEDICAL, INC. AND MAY NOT BE USED, REPRODUCED, PUBLISHED OR DISCLOSED TO OTHERS WITHOUT EXPRESSED WRITTEN AUTHORIZATION BY SYNAPSE BIOMEDICAL, INC. THIS DRAWING EMBODIES A CONFIDENTIAL, PROPRIETY DESIGN AND ALL DESIGN, MANUFACTURING USE AND SALES RIGHTS REGARDING SAME ARE EXPRESSLY RESERVED. | TOP SIDE FEATURES

through hole
top & bottom test pad with via
PCB trace
flex PCB only
rigid-flex PCB

NEAR FIELD COIL SIMULATION CONNECTION

CAUTION: VREC VOLTAGE WILL DESTROY
CIRCUIT IF APPLIED TO OTHER PINS

CUT FLEX AS CLOSE AS POSSIBLE TO THIS FLAP BEFORE FINAL ASSY

FLAP IS ADHERED TO COIL DURING FINAL ASSY FOR MECHANICAL STABILITY

APPROVALS | DATE

ENG: R. Yoder | 7-19-2018

DSN: K. Kowalski | 4-12-2022

PROJECT REVISION: * | DOCUMENT REVISION: * | DESIGN ITEM: *

CHK: T. Crish | 4-12-2022

TITLE
PCB Mechanical - Test Header
