COSMIIC-Inc/Implantables-PM-Hardware/NNP-DWG-115-004-000 PCB Files/NNP-DWG-115-004-000 PM2 Schematics/51-2001-01-5_04 Power Module Schematic.pdf

ECN | DESCRIPTION | REV | DATE | REV. SHT. DWG. NO.

# LR1 CUTOUT PLANES AND DO NOT ROUTE UNDERNEATH HIGH CURRENT SWITCHING LOOPS

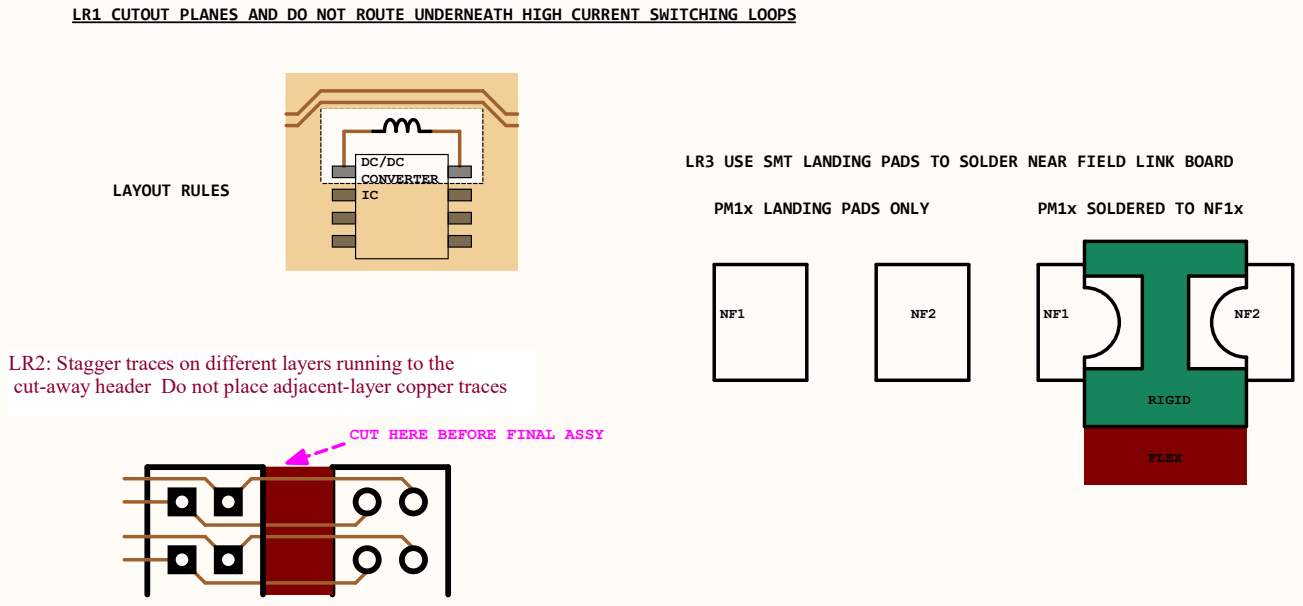
[picture p63: page 1]
51-2001-01-5_04.SchDoc; SIZE; DWG NO.; FILE NAME; SHEET; REV; SCALE:*; REFERENCE DOCUMENTS; BOM:; ASSY DWG:; FAB DWG:; PCB DWG:; FLEX; RIGID; PM1x LANDING PADS ONLY; PM1x SOLDERED TO NF1x; LAYOUT RULES; DC/DC CONVERTER IC

DWG. NO. | REV. | SHT.

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

LR3 USE SMT LANDING PADS TO SOLDER NEAR FIELD LINK BOARD

LR2: Stagger traces on different layers running to the
cut-away header Do not place adjacent-layer copper traces

CUT HERE BEFORE FINAL ASSY

APPROVALS | DATE

ENG: R. Yoder | 7-19-2018

DSN: K. Kowalski | 4-12-2022

PROJECT REVISION: * | DOCUMENT REVISION: * | DESIGN ITEM: *

CHK: T. Crish | 4-12-2022

TITLE
PCB Layout Rules
