COSMIIC-Inc/Implantables-PM-Hardware/NNP-DWG-115-004-000 PCB Files/NNP-DWG-115-004-000 PM2 Schematics/51-2001-01-7_04 Power Module Schematic.pdf

ECN | DESCRIPTION | REV | DATE | REV. SHT. DWG. NO.

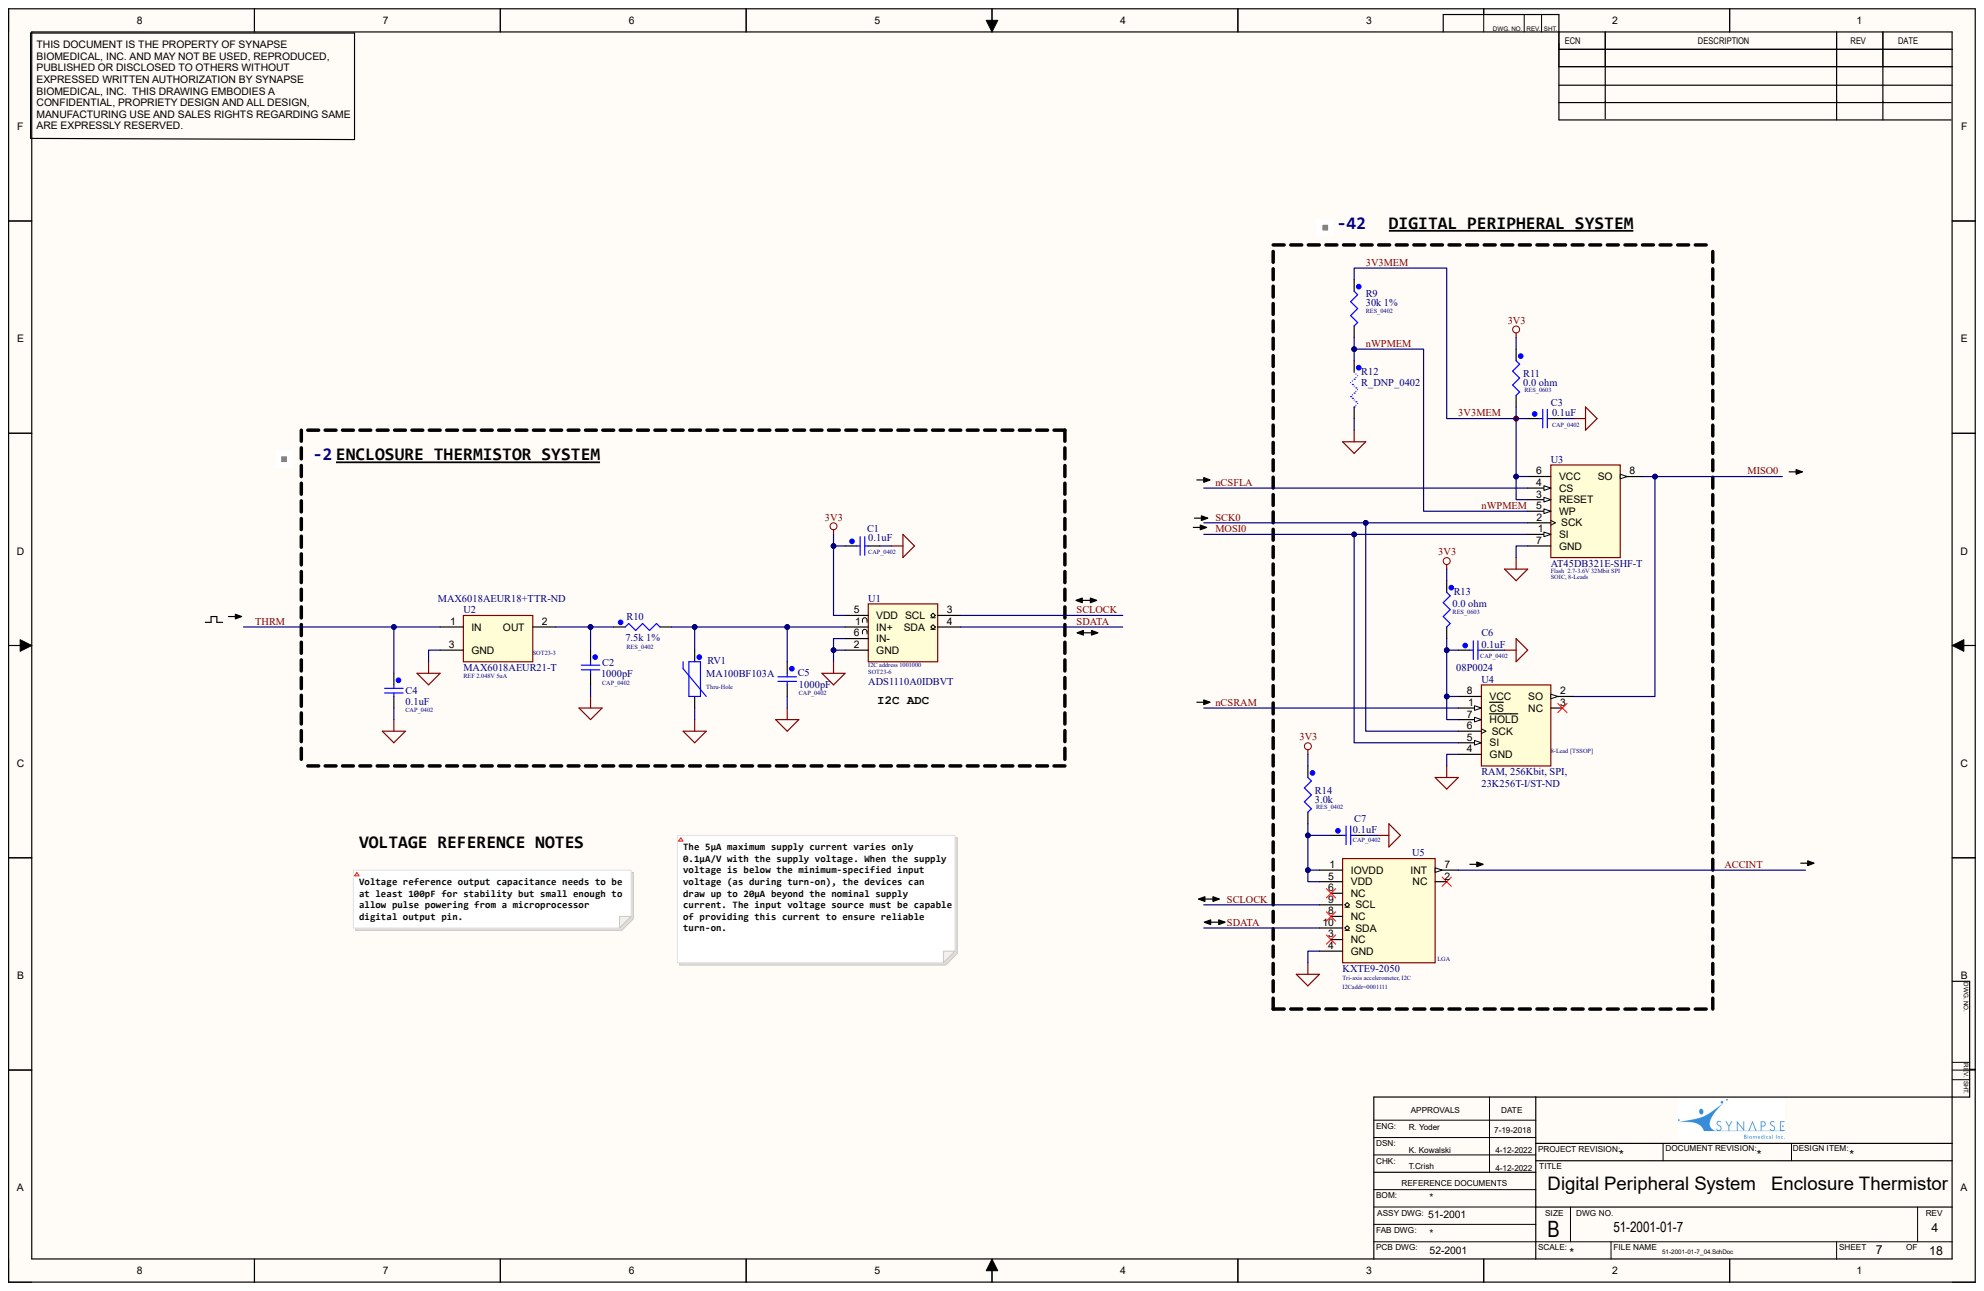
[picture p64: page 1]

DWG. NO. | REV. | SHT.

THIS DOCUMENT IS THE PROPERTY OF SYNAPSE BIOMEDICAL, INC. AND MAY NOT BE USED, REPRODUCED, PUBLISHED OR DISCLOSED TO OTHERS WITHOUT EXPRESSED WRITTEN AUTHORIZATION BY SYNAPSE BIOMEDICAL, INC. THIS DRAWING EMBODIES A CONFIDENTIAL, PROPRIETY DESIGN AND ALL DESIGN, MANUFACTURING USE AND SALES RIGHTS REGARDING SAME ARE EXPRESSLY RESERVED. | -42 DIGITAL PERIPHERAL SYSTEM

The 5μA maximum supply current varies only
0.1μA/V with the supply voltage. When the supply
voltage is below the minimum-specified input
voltage (as during turn-on), the devices can
draw up to 20μA beyond the nominal supply
current. The input voltage source must be capable
of providing this current to ensure reliable
turn-on.

Voltage reference output capacitance needs to be
at least 100pF for stability but small enough to
allow pulse powering from a microprocessor
digital output pin.

APPROVALS | DATE

ENG: R. Yoder | 7-19-2018

DSN: K. Kowalski | 4-12-2022

PROJECT REVISION: * | DOCUMENT REVISION: * | DESIGN ITEM: *

CHK: T.Crish | 4-12-2022

TITLE
Digital Peripheral System Enclosure Thermistor
