COSMIIC-Inc/Implantables-PM-Hardware/NNP-DWG-115-004-000 PCB Files/NNP-DWG-115-004-000 PM2 Schematics/51-2001-01-8_04 Power Module Schematic.pdf

ECN | DESCRIPTION | REV | DATE | REV. SHT. DWG. NO.

# -11 CPLD SYSTEM

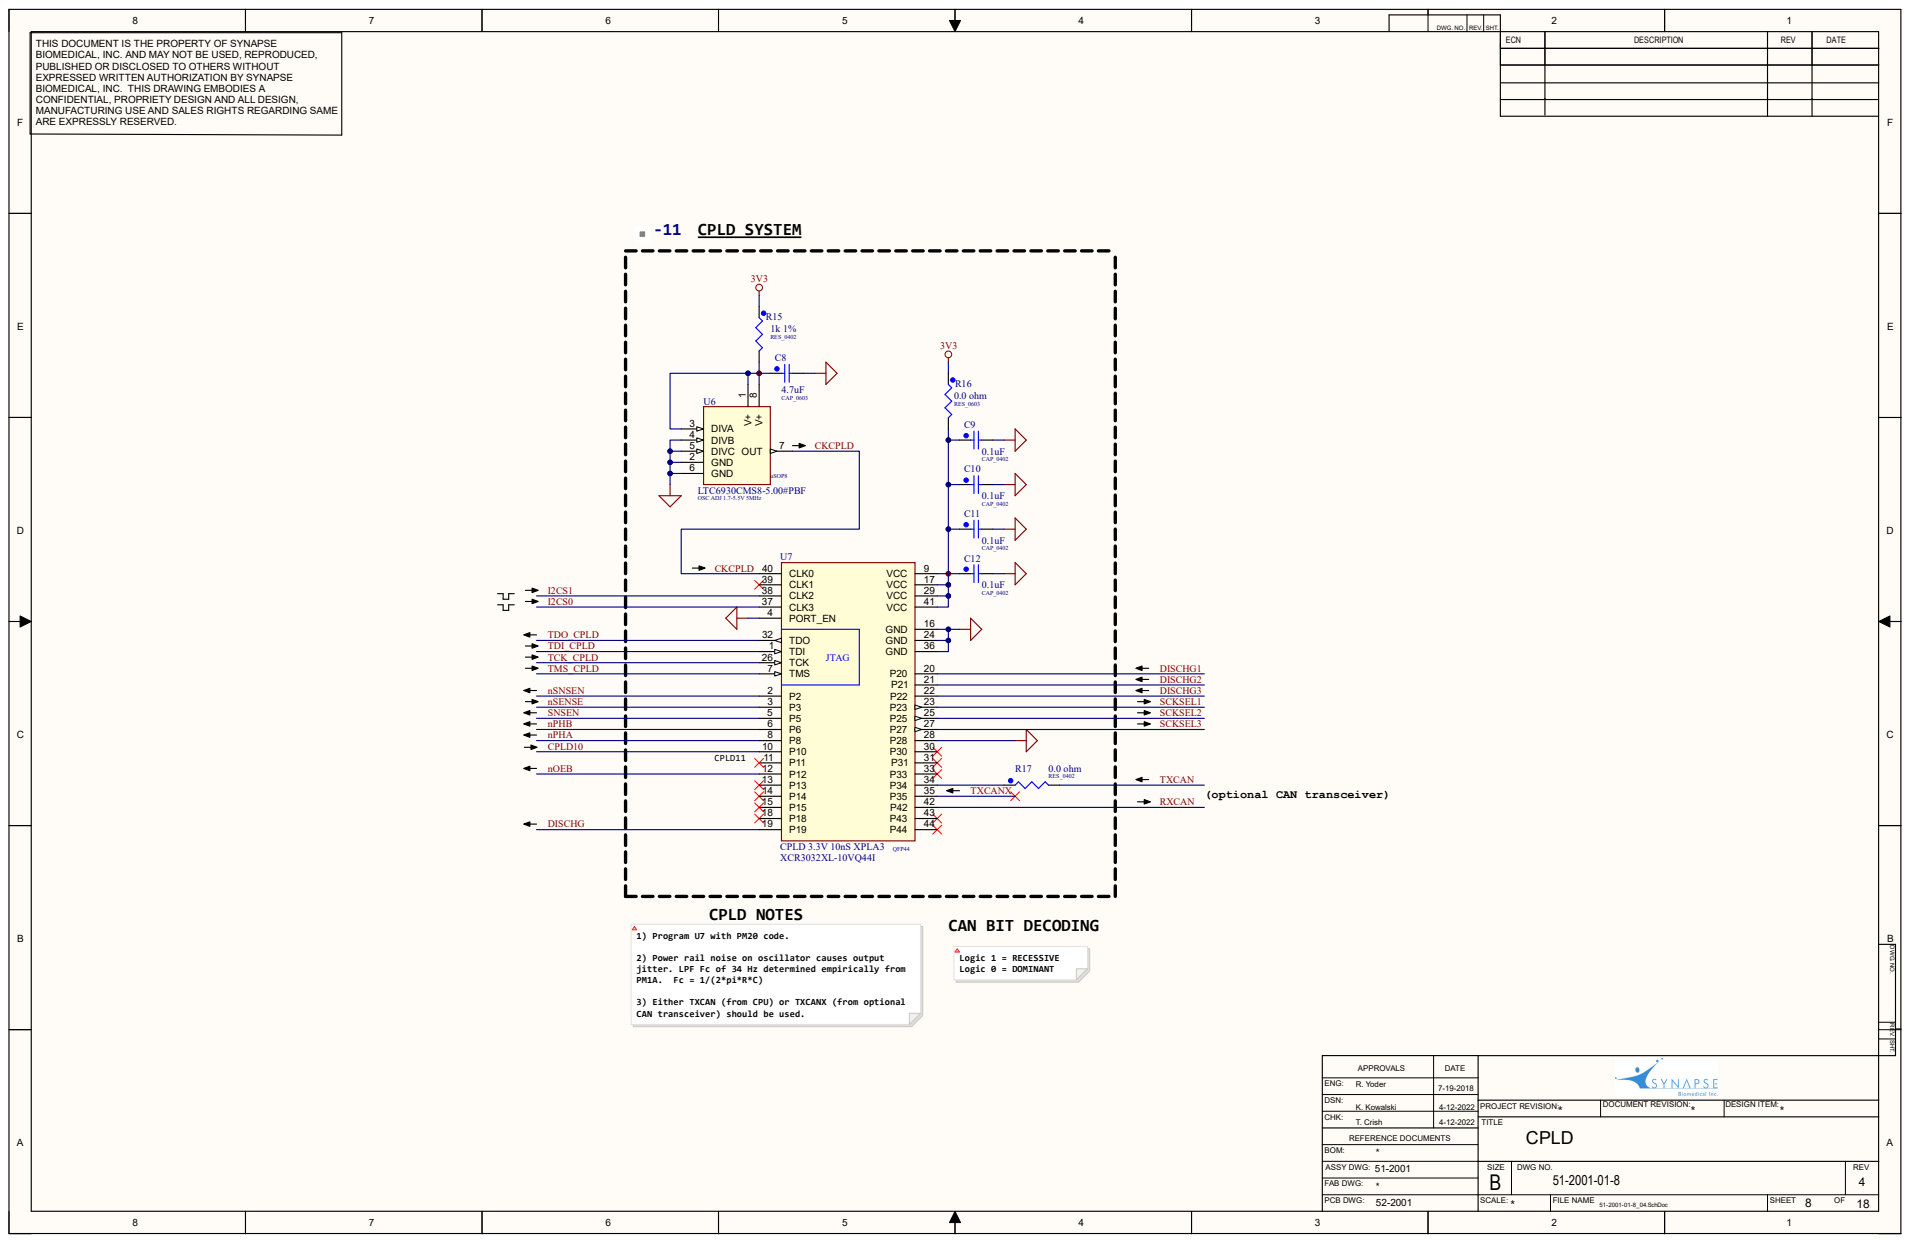
[picture p65: page 1]

DWG. NO. | REV. | SHT.

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

2) Power rail noise on oscillator causes output
jitter. LPF Fc of 34 Hz determined empirically from

3) Either TXCAN (from CPU) or TXCANX (from optional
CAN transceiver) should be used.

APPROVALS | DATE

ENG: R. Yoder | 7-19-2018

DSN: K. Kowalski | 4-12-2022

PROJECT REVISION: * | DOCUMENT REVISION: * | DESIGN ITEM: *

CHK: T. Crish | 4-12-2022
