COSMIIC-Inc/Implantables-PM-Hardware/NNP-DWG-115-004-000 PCB Files/NNP-DWG-115-004-000 PM2 Schematics/51-2001-01-9_04 Power Module Schematic.pdf

ECN | DESCRIPTION | REV | DATE | REV. SHT. DWG. NO.

# -12 NETWORK DRIVE SYSTEM

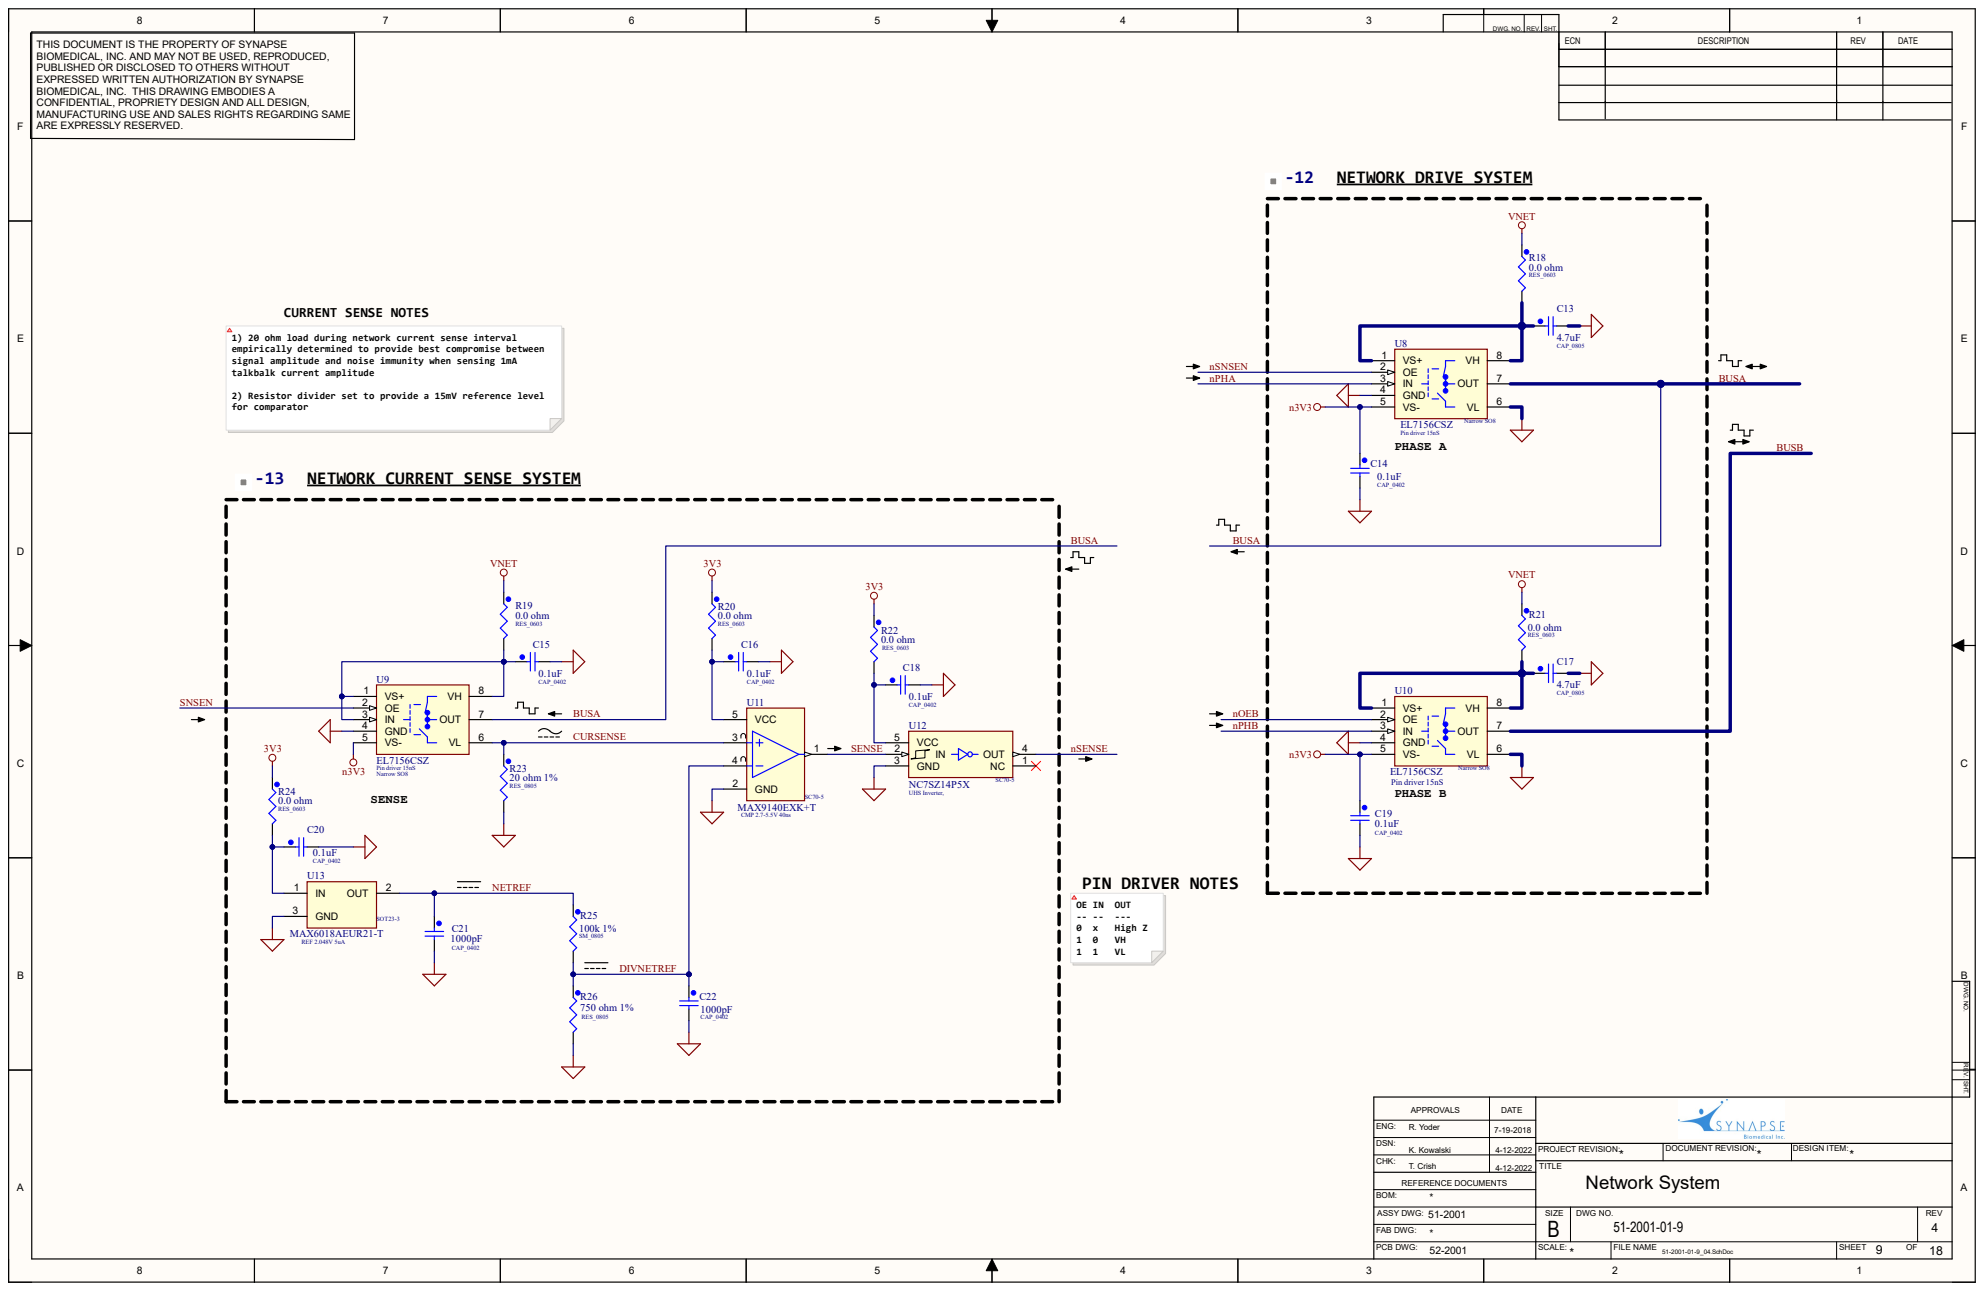
[picture p66: page 1]

DWG. NO. | REV. | SHT.

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

1) 20 ohm load during network current sense interval
empirically determined to provide best compromise between
signal amplitude and noise immunity when sensing 1mA
talkbalk current amplitude

2) Resistor divider set to provide a 15mV reference level
for comparator

-13 NETWORK CURRENT SENSE SYSTEM

APPROVALS | DATE

ENG: R. Yoder | 7-19-2018

DSN: K. Kowalski | 4-12-2022

PROJECT REVISION: * | DOCUMENT REVISION: * | DESIGN ITEM: *

CHK: T. Crish | 4-12-2022
