COSMIIC-Inc/Implantables-PM-Hardware/Mechanical Design CAD Files/Drawing PDFs/Exploded Power Module.pdf

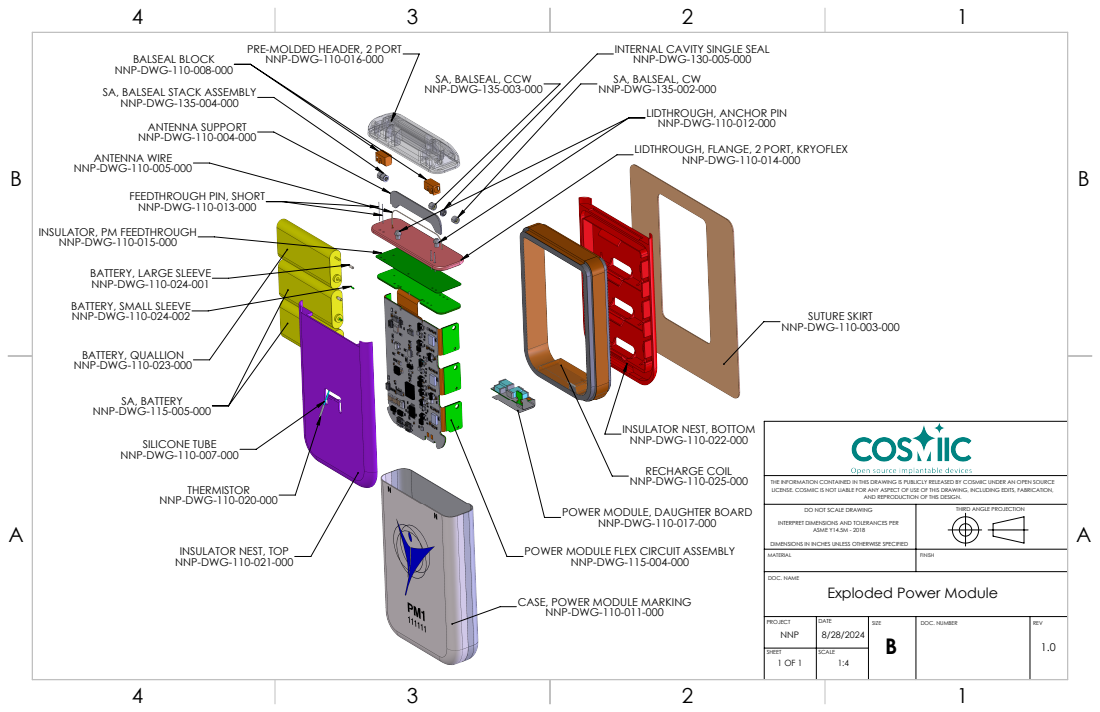
[picture p67: page 1]
SILICONE TUBE; SA, BATTERY; BATTERY, QUALLION; RECHARGE COIL; SUTURE SKIRT; DOC. NUMBER; REV; DOC. NAME; ASME Y14.5M - 2018; Exploded Power Module

PRE-MOLDED HEADER, 2 PORT
NNP-DWG-110-016-000

INTERNAL CAVITY SINGLE SEAL
NNP-DWG-130-005-000
SA, BALSEAL, CW
NNP-DWG-135-002-000

BALSEAL BLOCK
NNP-DWG-110-008-000
SA, BALSEAL STACK ASSEMBLY
NNP-DWG-135-004-000
ANTENNA SUPPORT
NNP-DWG-110-004-000
ANTENNA WIRE
NNP-DWG-110-005-000

SA, BALSEAL, CCW
NNP-DWG-135-003-000

LIDTHROUGH, ANCHOR PIN
NNP-DWG-110-012-000
LIDTHROUGH, FLANGE, 2 PORT, KRYOFLEX

FEEDTHROUGH PIN, SHORT
NNP-DWG-110-013-000

INSULATOR, PM FEEDTHROUGH
NNP-DWG-110-015-000

BATTERY, LARGE SLEEVE
NNP-DWG-110-024-001
BATTERY, SMALL SLEEVE
NNP-DWG-110-024-002

INSULATOR NEST, BOTTOM
NNP-DWG-110-022-000

THE INFORMATION CONTAINED IN THIS DRAWING IS PUBLICLY RELEASED BY COSMIIC UNDER AN OPEN SOURCE
LICENSE. COSMIIC IS NOT LIABLE FOR ANY ASPECT OF USE OF THIS DRAWING, INCLUDING EDITS, FABRICATION,

AND REPRODUCTION OF THIS DESIGN.

POWER MODULE, DAUGHTER BOARD
NNP-DWG-110-017-000

DO NOT SCALE DRAWING

THIRD ANGLE PROJECTION

INTERPRET DIMENSIONS AND TOLERANCES PER

DIMENSIONS IN INCHES UNLESS OTHERWISE SPECIFIED

INSULATOR NEST, TOP
NNP-DWG-110-021-000

POWER MODULE FLEX CIRCUIT ASSEMBLY

CASE, POWER MODULE MARKING
NNP-DWG-110-011-000
