COSMIIC-Inc/Implantables-PM-Hardware/Mechanical Design CAD Files/Drawing PDFs/NNP-DWG-110-010-000 Case, Trimmed.pdf

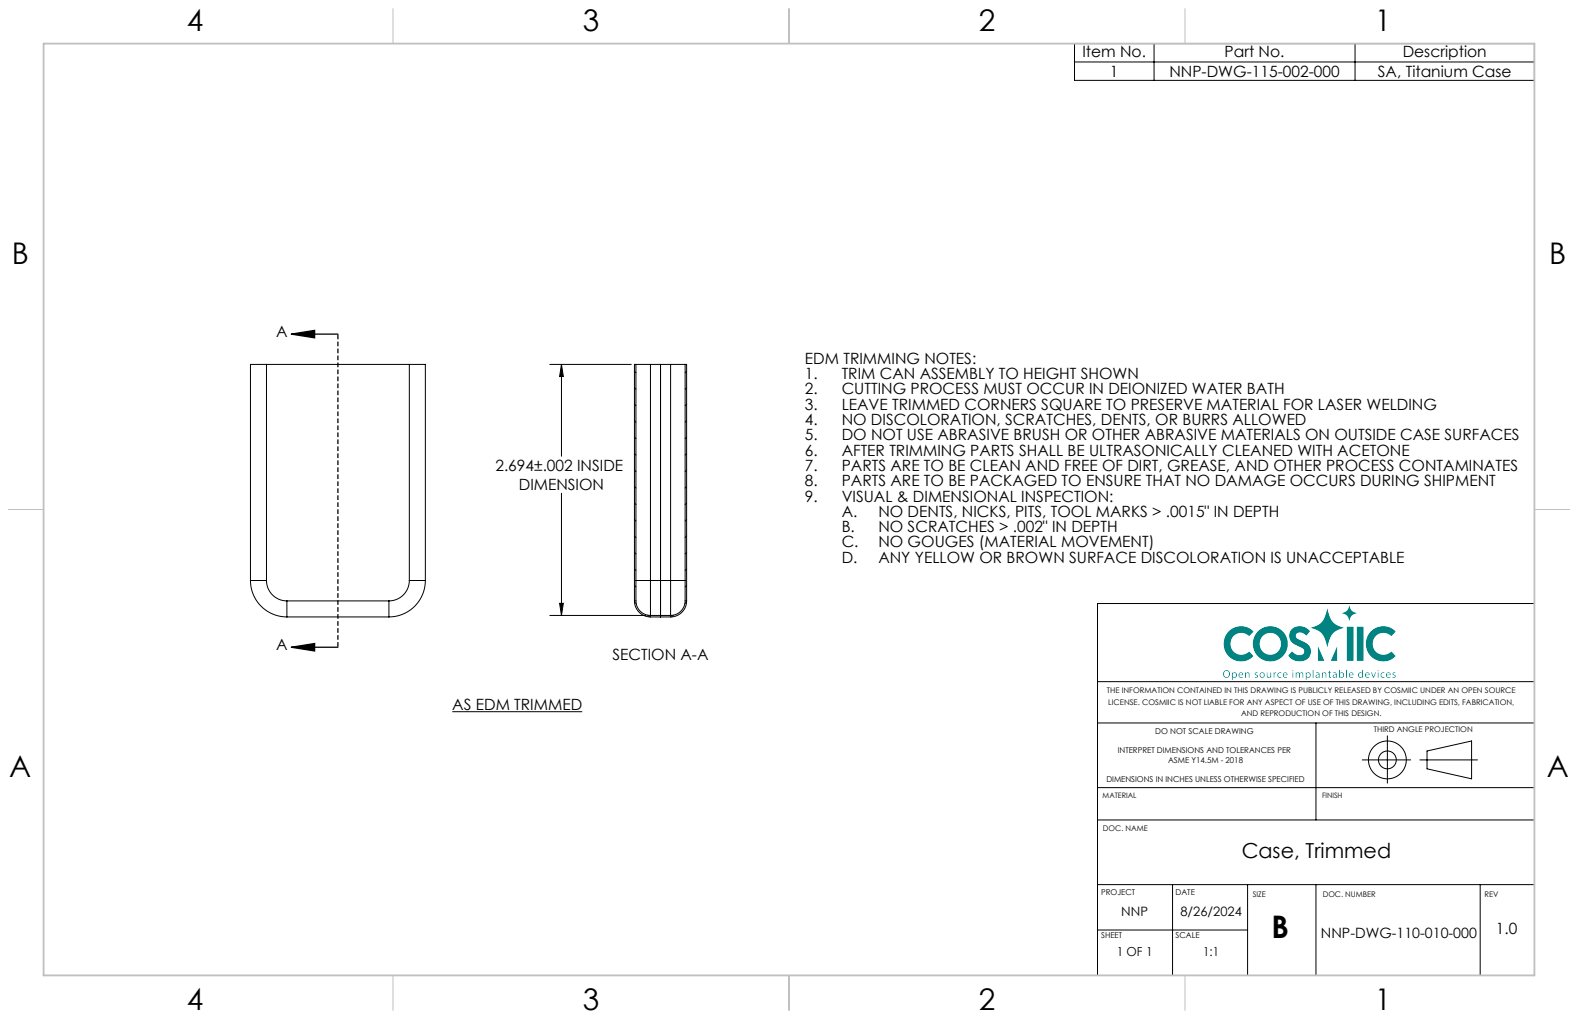
[picture p69: page 1]
2.694±.002 INSIDE; SECTION A-A; DOC. NUMBER; REV; DOC. NAME; ASME Y14.5M - 2018; Case, Trimmed

Item No. | Part No. | Description
1 | NNP-DWG-115-002-000 | SA, Titanium Case

EDM TRIMMING NOTES:
1. TRIM CAN ASSEMBLY TO HEIGHT SHOWN
2. CUTTING PROCESS MUST OCCUR IN DEIONIZED WATER BATH
3. LEAVE TRIMMED CORNERS SQUARE TO PRESERVE MATERIAL FOR LASER WELDING
4. NO DISCOLORATION, SCRATCHES, DENTS, OR BURRS ALLOWED
5. DO NOT USE ABRASIVE BRUSH OR OTHER ABRASIVE MATERIALS ON OUTSIDE CASE SURFACES
6. AFTER TRIMMING PARTS SHALL BE ULTRASONICALLY CLEANED WITH ACETONE
7. PARTS ARE TO BE CLEAN AND FREE OF DIRT, GREASE, AND OTHER PROCESS CONTAMINATES
8. PARTS ARE TO BE PACKAGED TO ENSURE THAT NO DAMAGE OCCURS DURING SHIPMENT
9. VISUAL & DIMENSIONAL INSPECTION:
A. NO DENTS, NICKS, PITS, TOOL MARKS > .0015" IN DEPTH
B. NO SCRATCHES > .002" IN DEPTH
C. NO GOUGES (MATERIAL MOVEMENT)
D. ANY YELLOW OR BROWN SURFACE DISCOLORATION IS UNACCEPTABLE

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

AS EDM TRIMMED

AND REPRODUCTION OF THIS DESIGN.

DO NOT SCALE DRAWING

THIRD ANGLE PROJECTION

INTERPRET DIMENSIONS AND TOLERANCES PER

DIMENSIONS IN INCHES UNLESS OTHERWISE SPECIFIED
