COSMIIC-Inc/Implantables-PM-Hardware/Mechanical Design CAD Files/Drawing PDFs/NNP-DWG-115-005-000 SA, Battery.pdf

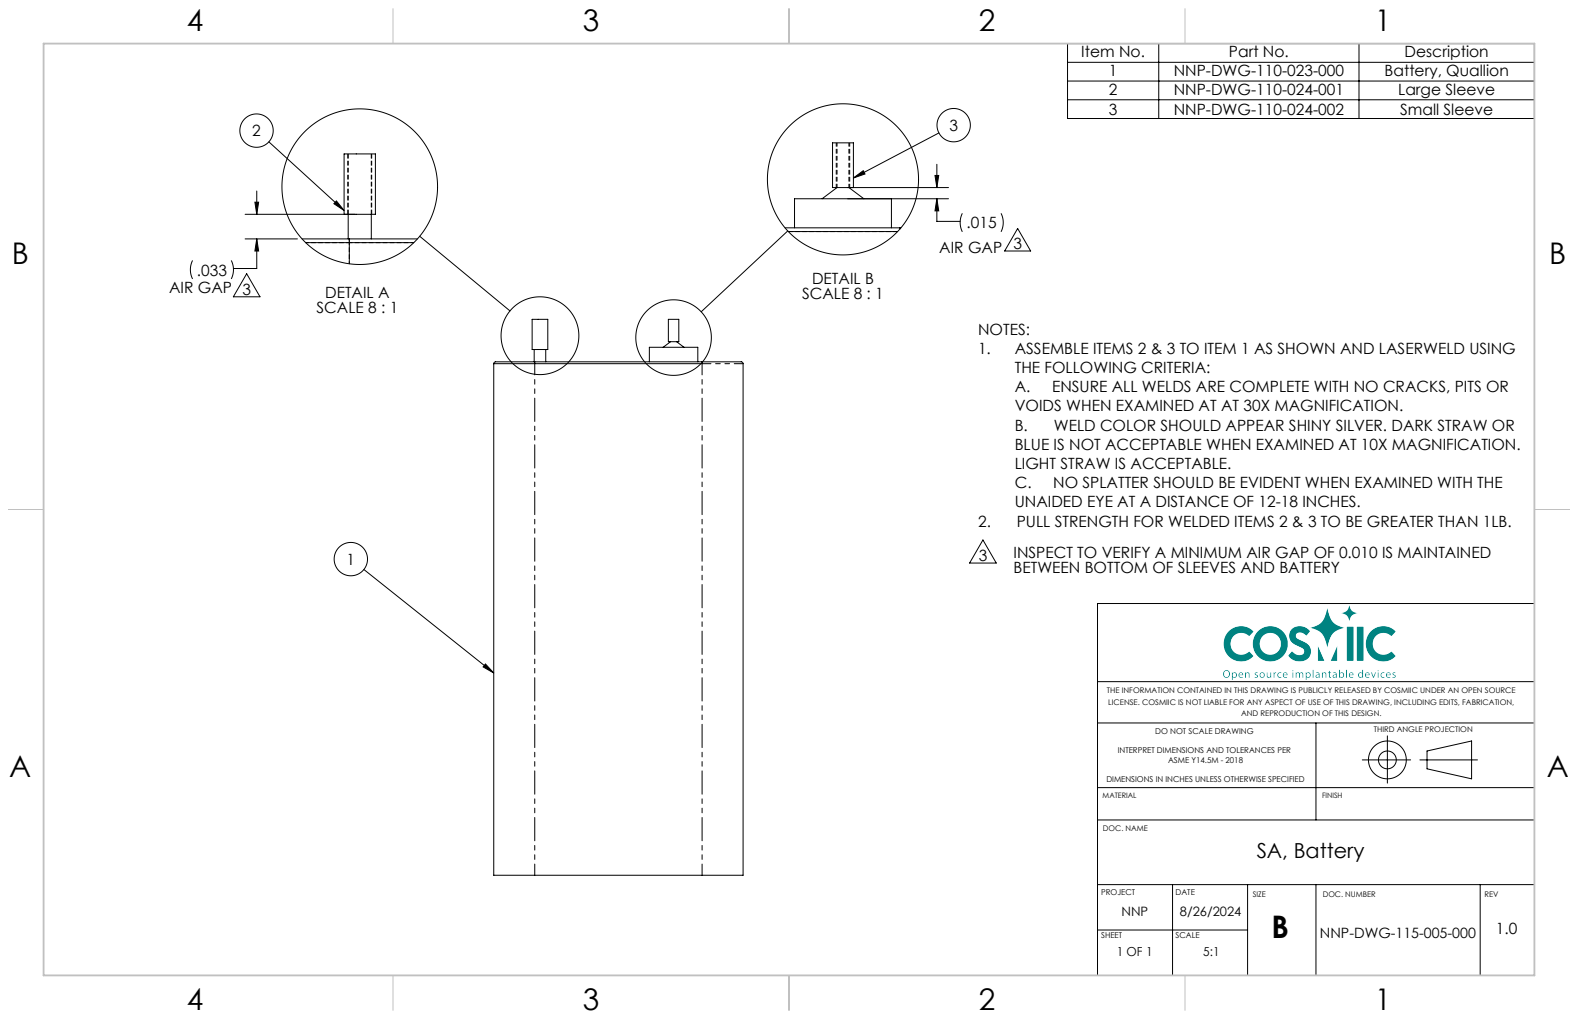
[picture p71: page 1]
DETAIL A SCALE 8 : 1; DETAIL B SCALE 8 : 1; AIR GAP; INSPECT TO VERIFY A MINIMUM AIR GAP OF 0.010 IS MAINTAINED; DOC. NUMBER; REV; DOC. NAME; ASME Y14.5M - 2018; SA, Battery

Item No. | Part No. | Description
1 | NNP-DWG-110-023-000 | Battery, Quallion
2 | NNP-DWG-110-024-001 | Large Sleeve
3 | NNP-DWG-110-024-002 | Small Sleeve

NOTES:
1. ASSEMBLE ITEMS 2 & 3 TO ITEM 1 AS SHOWN AND LASERWELD USING
THE FOLLOWING CRITERIA:
A. ENSURE ALL WELDS ARE COMPLETE WITH NO CRACKS, PITS OR
VOIDS WHEN EXAMINED AT AT 30X MAGNIFICATION.
B. WELD COLOR SHOULD APPEAR SHINY SILVER. DARK STRAW OR
BLUE IS NOT ACCEPTABLE WHEN EXAMINED AT 10X MAGNIFICATION.
LIGHT STRAW IS ACCEPTABLE.
C. NO SPLATTER SHOULD BE EVIDENT WHEN EXAMINED WITH THE
UNAIDED EYE AT A DISTANCE OF 12-18 INCHES.
2. PULL STRENGTH FOR WELDED ITEMS 2 & 3 TO BE GREATER THAN 1LB.
BETWEEN BOTTOM OF SLEEVES AND BATTERY

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

AND REPRODUCTION OF THIS DESIGN.

DO NOT SCALE DRAWING

THIRD ANGLE PROJECTION

INTERPRET DIMENSIONS AND TOLERANCES PER

DIMENSIONS IN INCHES UNLESS OTHERWISE SPECIFIED
