COSMIIC-Inc/Implantables-PM-Hardware/Mechanical Design CAD Files/Drawing PDFs/NNP-DWG-115-006-000 Power Module Coil Assembly.pdf

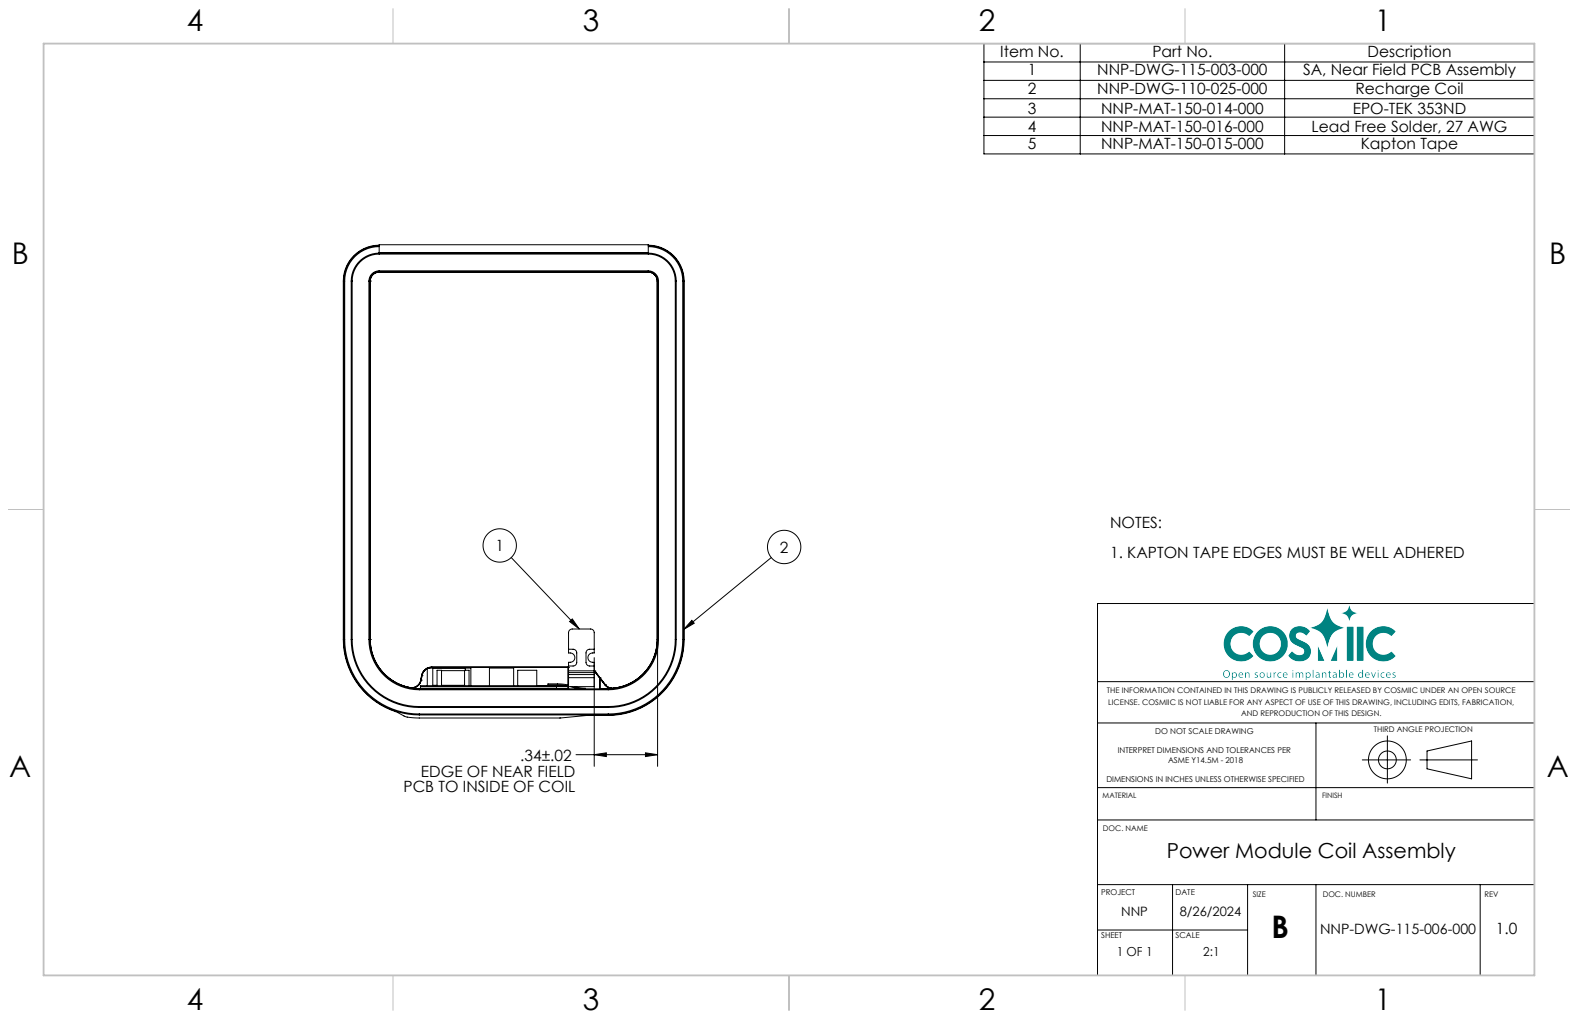
[picture p72: page 1]
DOC. NUMBER; REV; DOC. NAME; ASME Y14.5M - 2018

Item No. | Part No. | Description
1 | NNP-DWG-115-003-000 | SA, Near Field PCB Assembly
2 | NNP-DWG-110-025-000 | Recharge Coil
3 | NNP-MAT-150-014-000 | EPO-TEK 353ND
4 | NNP-MAT-150-016-000 | Lead Free Solder, 27 AWG
5 | NNP-MAT-150-015-000 | Kapton Tape

NOTES:
1. KAPTON TAPE EDGES MUST BE WELL ADHERED

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

AND REPRODUCTION OF THIS DESIGN.

DO NOT SCALE DRAWING

THIRD ANGLE PROJECTION

INTERPRET DIMENSIONS AND TOLERANCES PER

EDGE OF NEAR FIELD
PCB TO INSIDE OF COIL

DIMENSIONS IN INCHES UNLESS OTHERWISE SPECIFIED
Power Module Coil Assembly
NNP-DWG-115-006-000
