COSMIIC-Inc/Implantables-PM-Hardware/Mechanical Design CAD Files/Drawing PDFs/NNP-DWG-115-008-000 Power Module Header Assembly, 2 Port.pdf

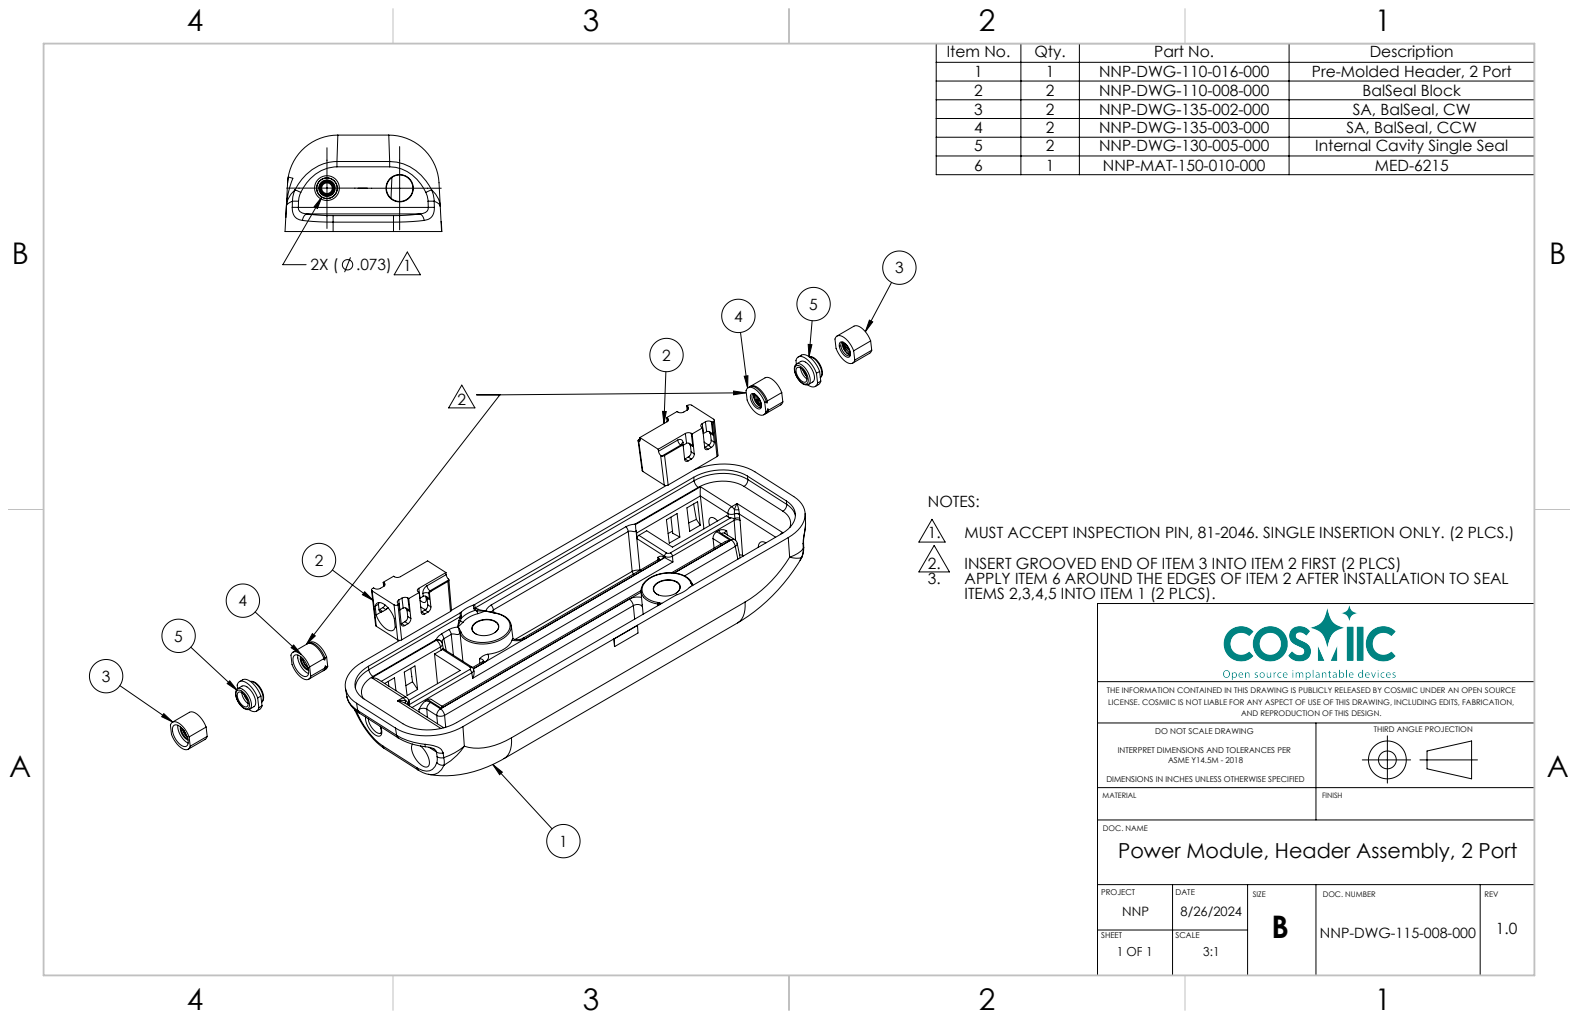
[picture p73: page 1]
DOC. NUMBER; REV; DOC. NAME; ASME Y14.5M - 2018

Item No. | Qty. | Part No. | Description
1 | 1 | NNP-DWG-110-016-000 | Pre-Molded Header, 2 Port
2 | 2 | NNP-DWG-110-008-000 | BalSeal Block
3 | 2 | NNP-DWG-135-002-000 | SA, BalSeal, CW
4 | 2 | NNP-DWG-135-003-000 | SA, BalSeal, CCW
5 | 2 | NNP-DWG-130-005-000 | Internal Cavity Single Seal
6 | 1 | NNP-MAT-150-010-000 | MED-6215

NOTES:
1. MUST ACCEPT INSPECTION PIN, 81-2046. SINGLE INSERTION ONLY. (2 PLCS.)
2. INSERT GROOVED END OF ITEM 3 INTO ITEM 2 FIRST (2 PLCS)
3. APPLY ITEM 6 AROUND THE EDGES OF ITEM 2 AFTER INSTALLATION TO SEAL
ITEMS 2,3,4,5 INTO ITEM 1 (2 PLCS).

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

AND REPRODUCTION OF THIS DESIGN.

DO NOT SCALE DRAWING

THIRD ANGLE PROJECTION

INTERPRET DIMENSIONS AND TOLERANCES PER

DIMENSIONS IN INCHES UNLESS OTHERWISE SPECIFIED
Power Module, Header Assembly, 2 Port
