COSMIIC-Inc/Implantables-PM-Hardware/Mechanical Design CAD Files/Drawing PDFs/NNP-DWG-130-015-000 Drawing, BalSeal - Definition of Spring Direction.pdf

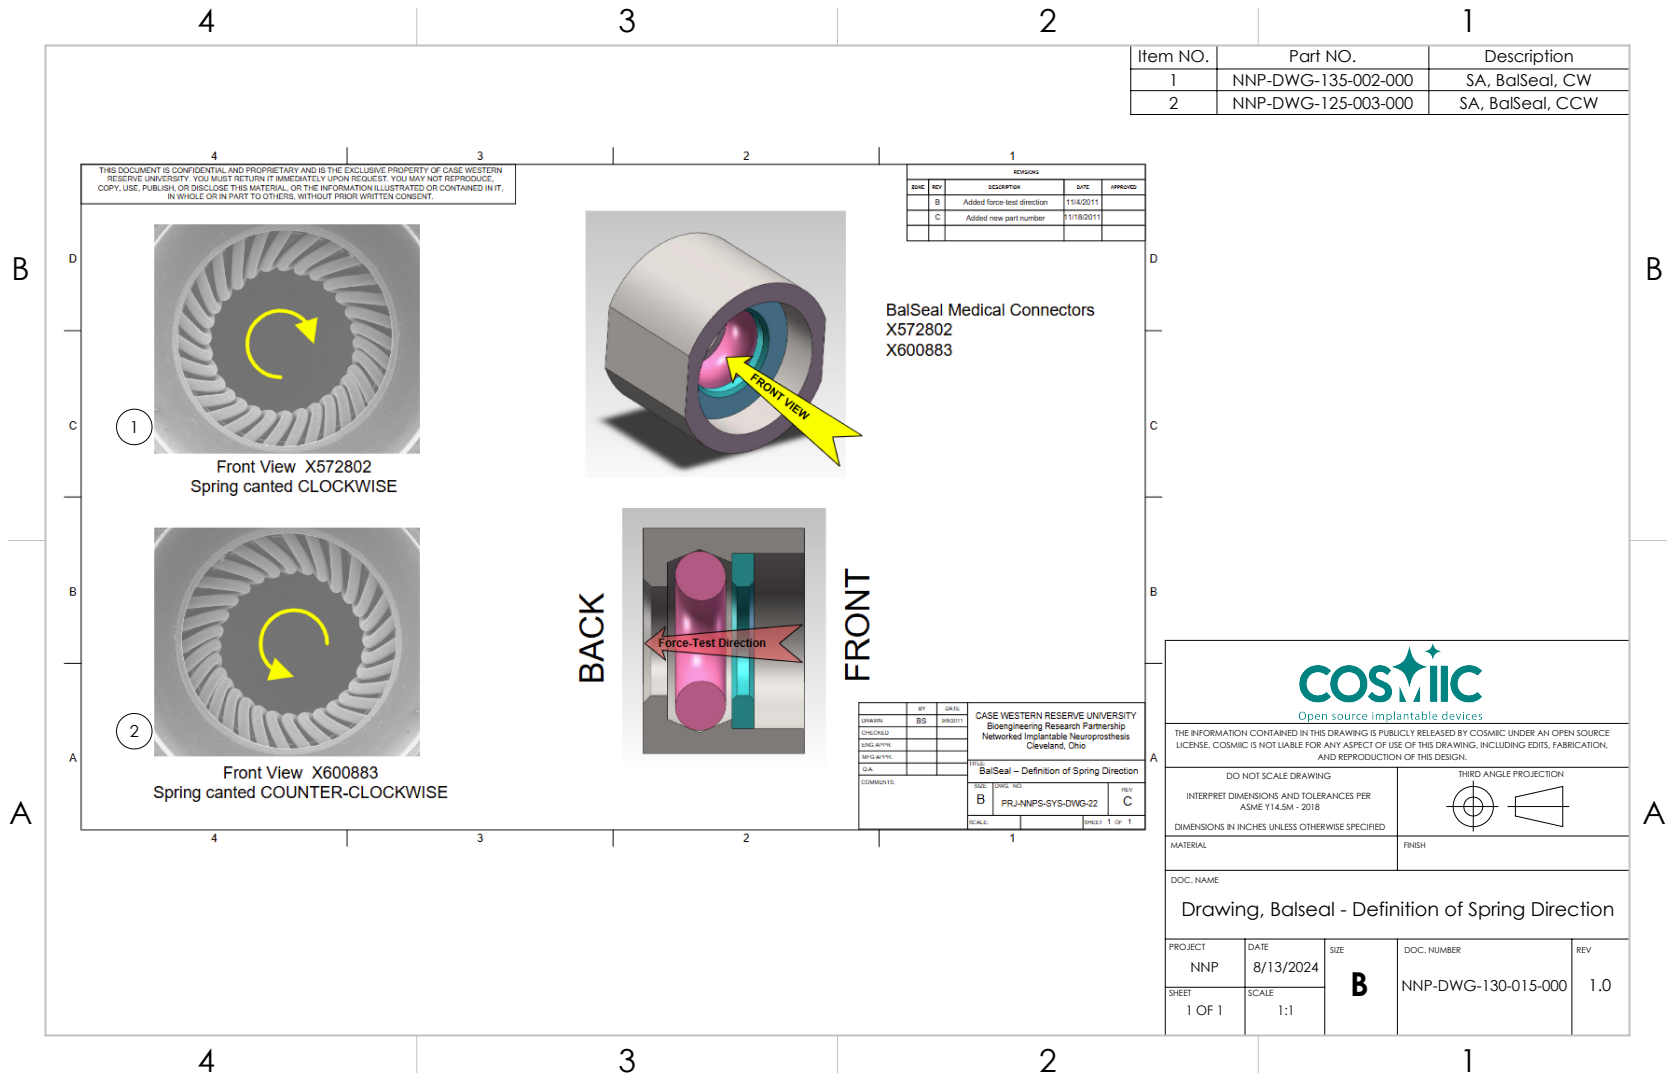
[picture p77: page 1]
DOC. NUMBER; REV; ASME Y14.5M - 2018

Item NO. | Part NO. | Description
1 | NNP-DWG-135-002-000 | SA, BalSeal, CW
2 | NNP-DWG-125-003-000 | SA, BalSeal, CCW

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

AND REPRODUCTION OF THIS DESIGN.

DO NOT SCALE DRAWING

THIRD ANGLE PROJECTION

INTERPRET DIMENSIONS AND TOLERANCES PER

DIMENSIONS IN INCHES UNLESS OTHERWISE SPECIFIED

DOC. NAME
Drawing, Balseal - Definition of Spring Direction
